Wakoma/nimble/assets/img/2-21.jpg

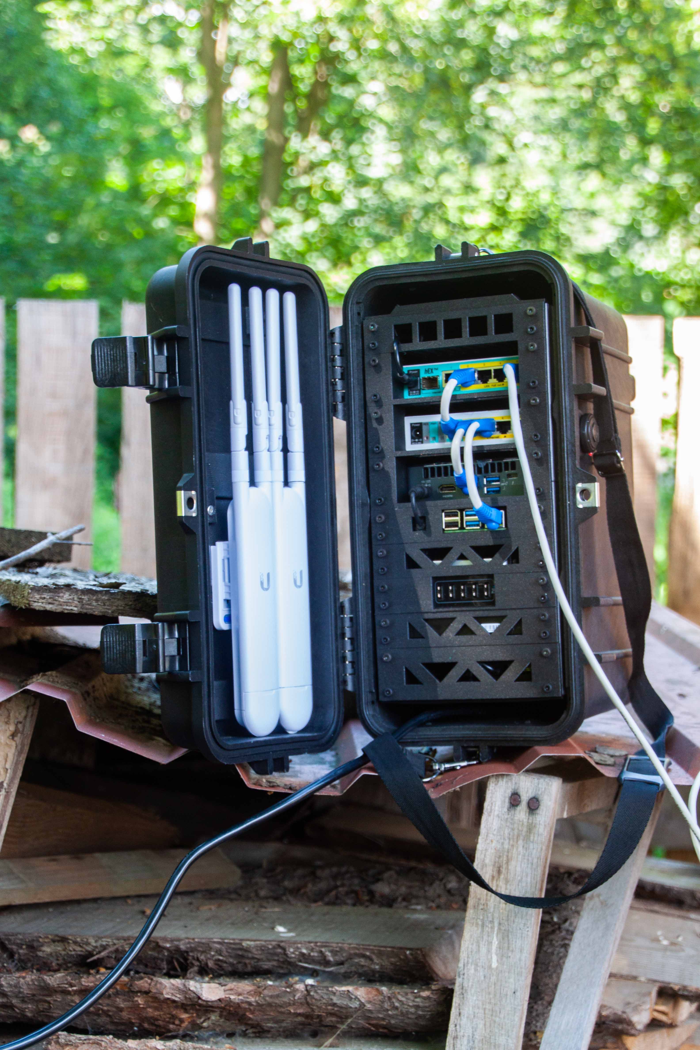
assets/img/2-21.jpg
