Wakoma/nimble/assets/img/3-4.jpg

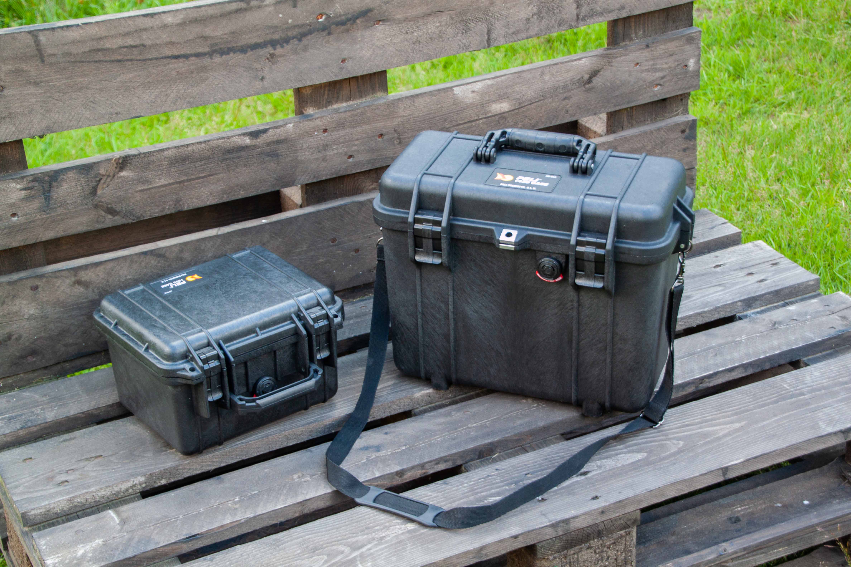
assets/img/3-4.jpg
