Wakoma/nimble/assets/img/12.jpg

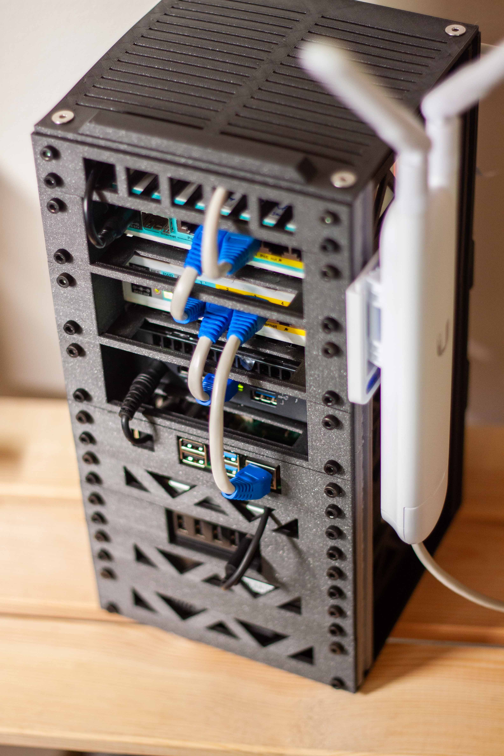
assets/img/12.jpg
