Wakoma/nimble/assets/img/16.jpg

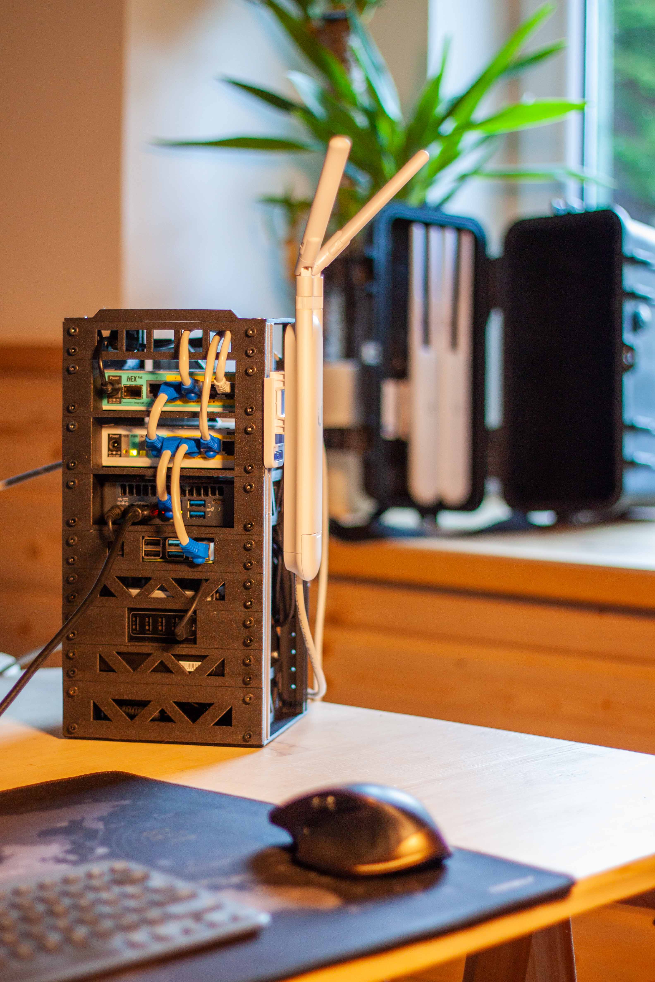
assets/img/16.jpg
