Wakoma/nimble/assets/img/18.jpg

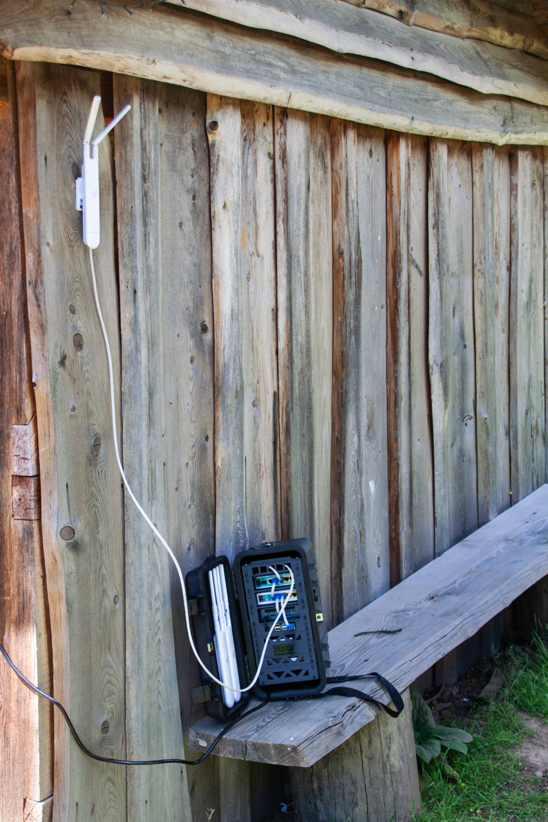
assets/img/18.jpg
