Wakoma/nimble/assets/img/LibreRouter/Carrousel-web/2.png

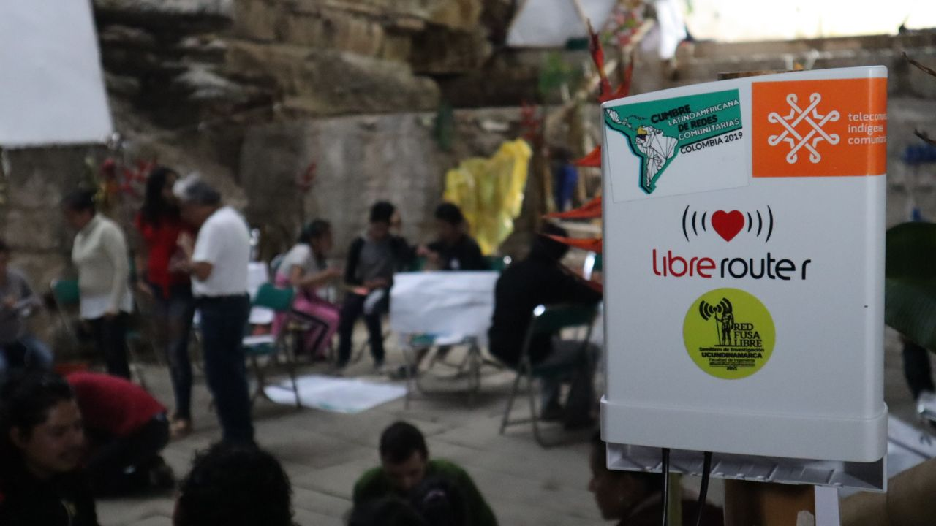
assets/img/LibreRouter/Carrousel-web/2.png
