Wakoma/nimble/assets/img/LibreRouter/Carrousel-web/3.png

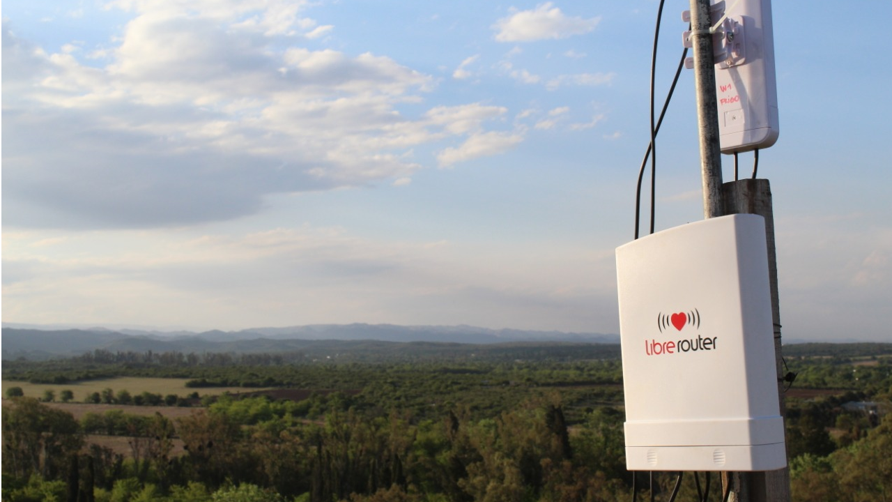
assets/img/LibreRouter/Carrousel-web/3.png
