Wakoma/nimble/assets/img/LibreRouter/Carrousel-web/5.png

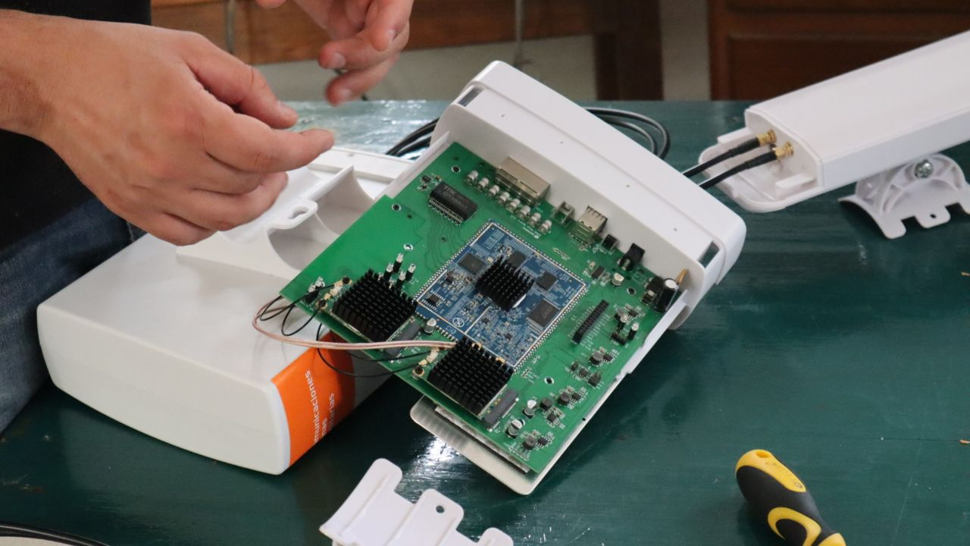
assets/img/LibreRouter/Carrousel-web/5.png
