Wakoma/nimble/assets/img/LibreRouter/Carrousel-web/6.png

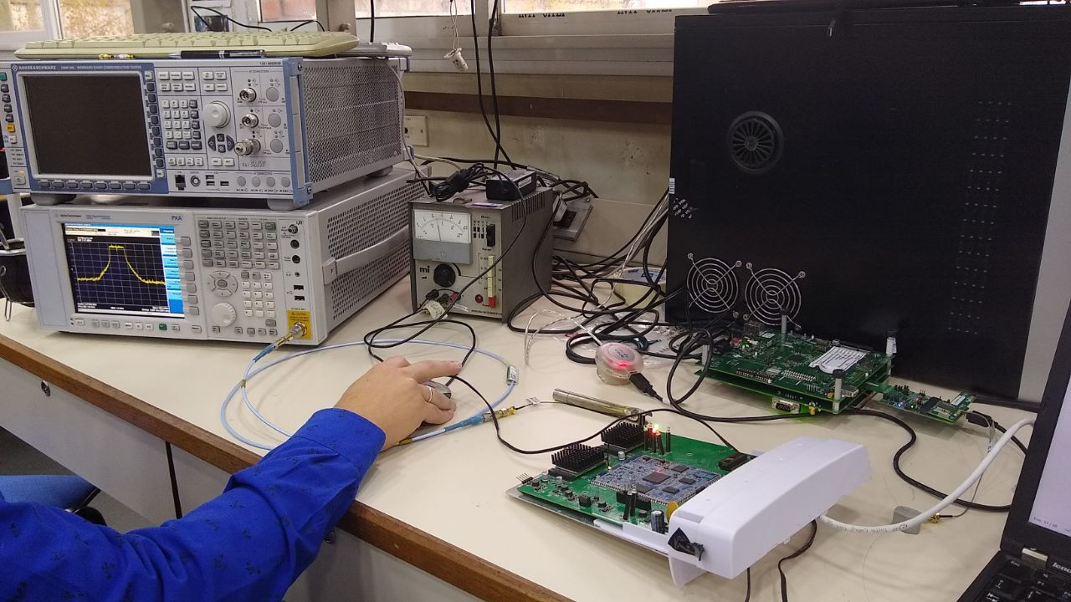
assets/img/LibreRouter/Carrousel-web/6.png
