Wakoma/nimble/assets/img/mesh.jpg

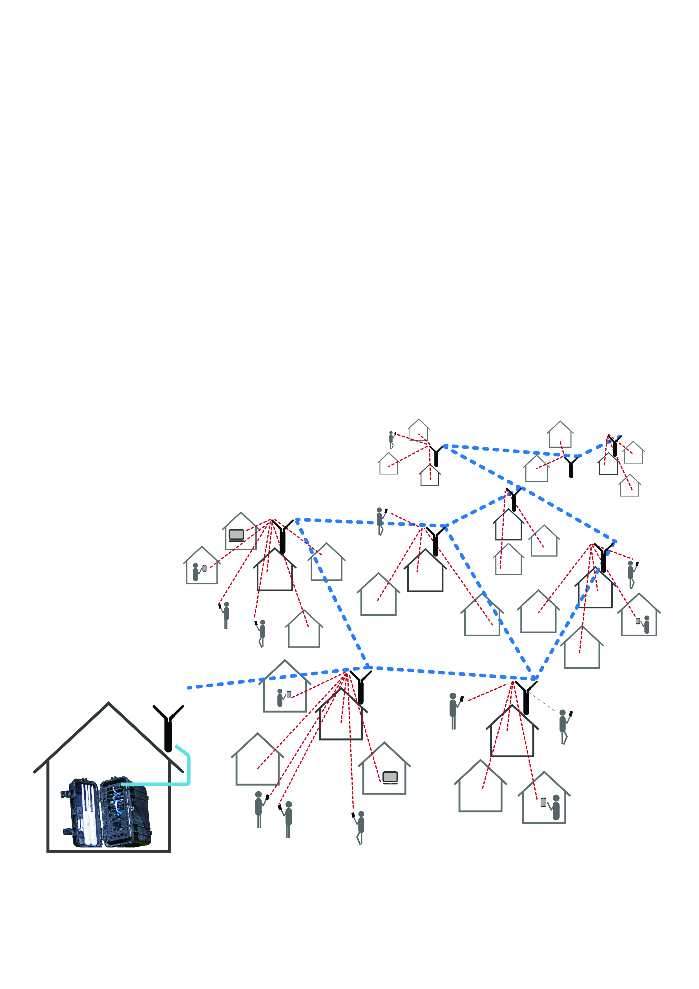
assets/img/mesh.jpg
