Wakoma/nimble/assets/img/Model_M/2.jpg

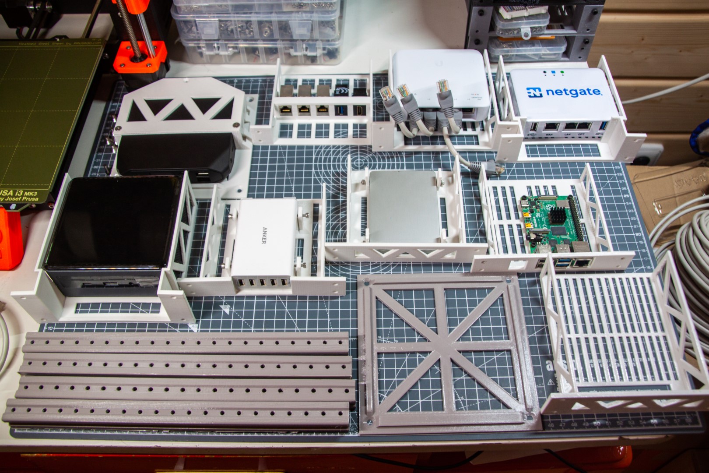
assets/img/Model_M/2.jpg
