Wakoma/nimble/assets/img/Model_M/3.jpg

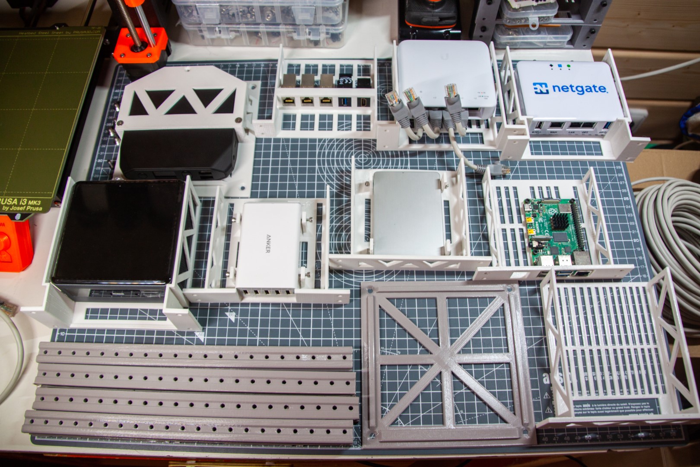
assets/img/Model_M/3.jpg
