Wakoma/nimble/assets/img/Model_M/4.jpg

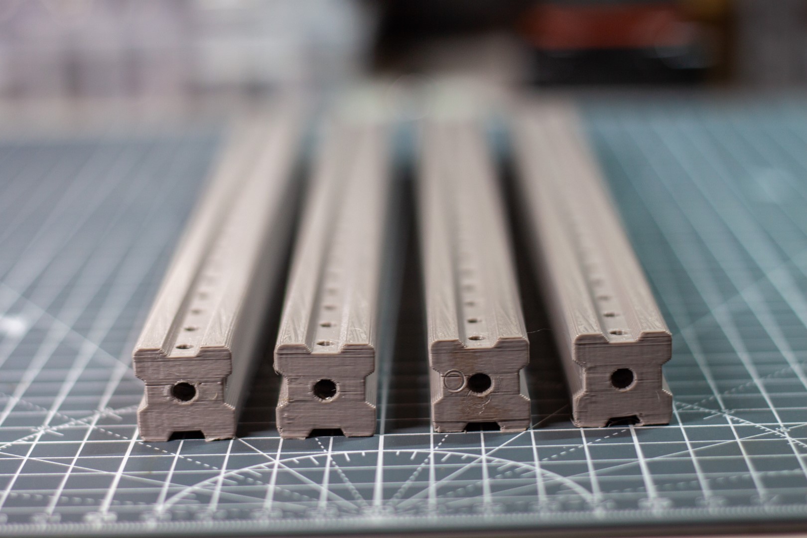
assets/img/Model_M/4.jpg
