Wakoma/nimble/assets/img/Model_M/5.jpg

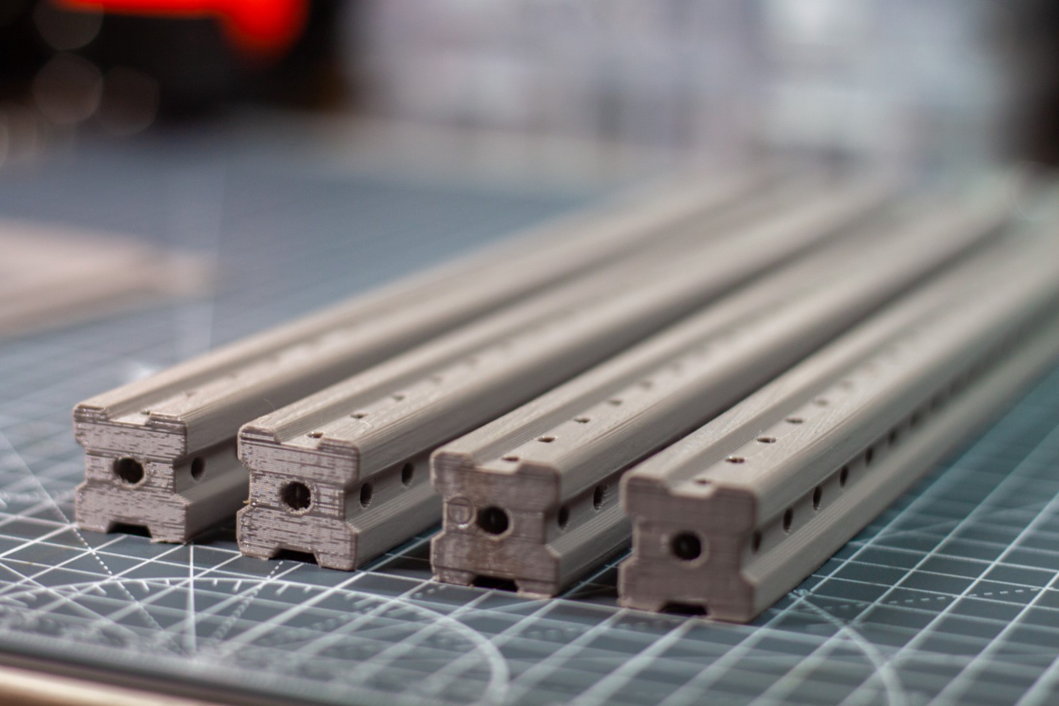
assets/img/Model_M/5.jpg
