Wakoma/nimble/assets/img/Model_M/6.jpg

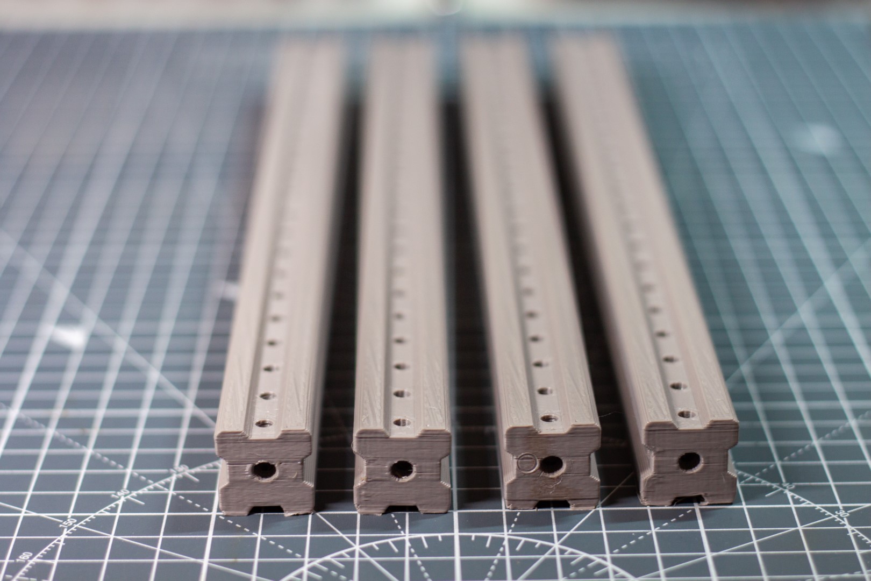
assets/img/Model_M/6.jpg
