Wakoma/nimble/assets/img/Model_M/7.jpg

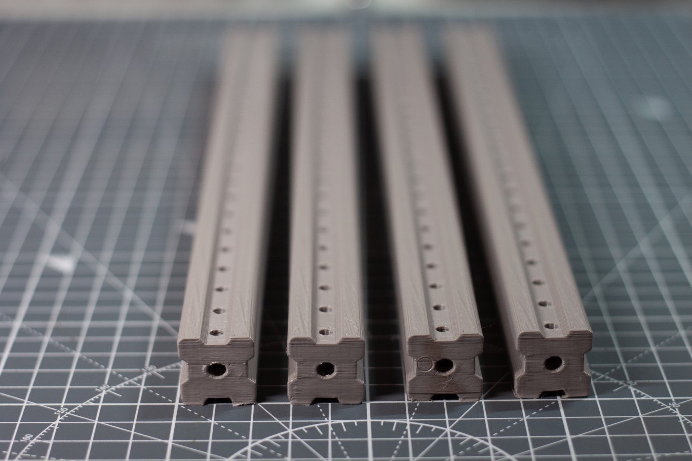
assets/img/Model_M/7.jpg
