Wakoma/nimble/assets/img/Model_M/8.jpg

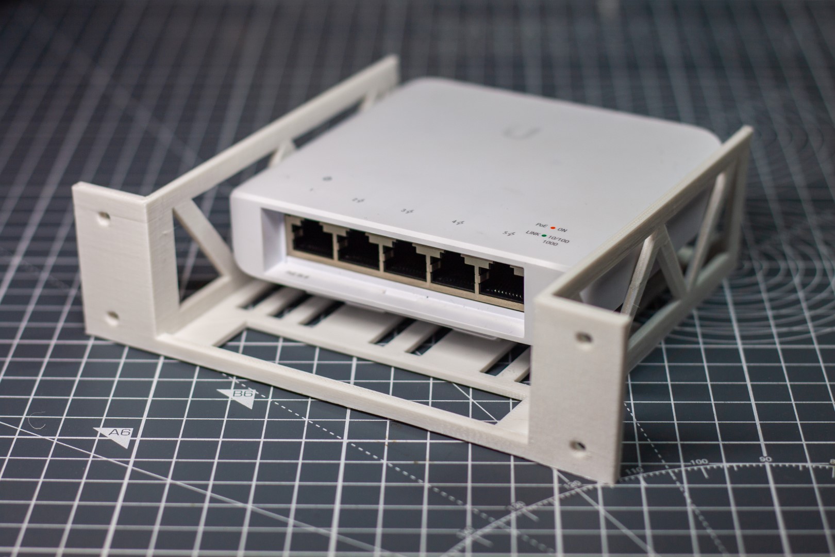
assets/img/Model_M/8.jpg
