Wakoma/nimble/assets/img/Model_M/9.jpg

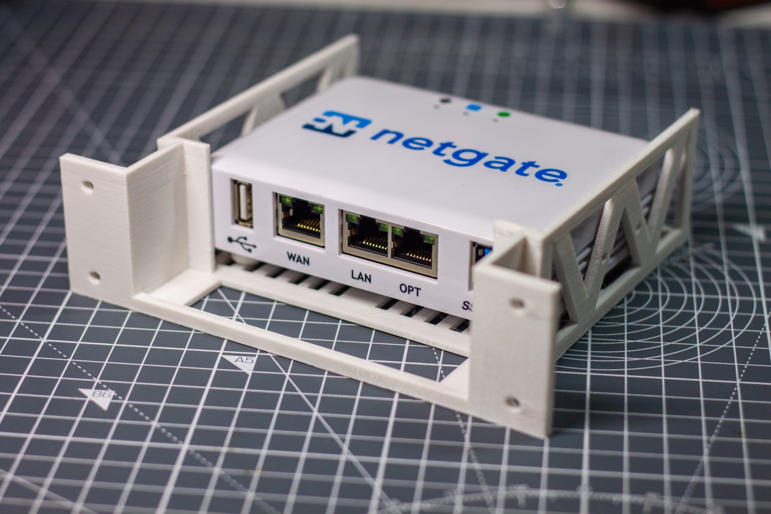
assets/img/Model_M/9.jpg
