Wakoma/nimble/assets/img/Model_M/10.jpg

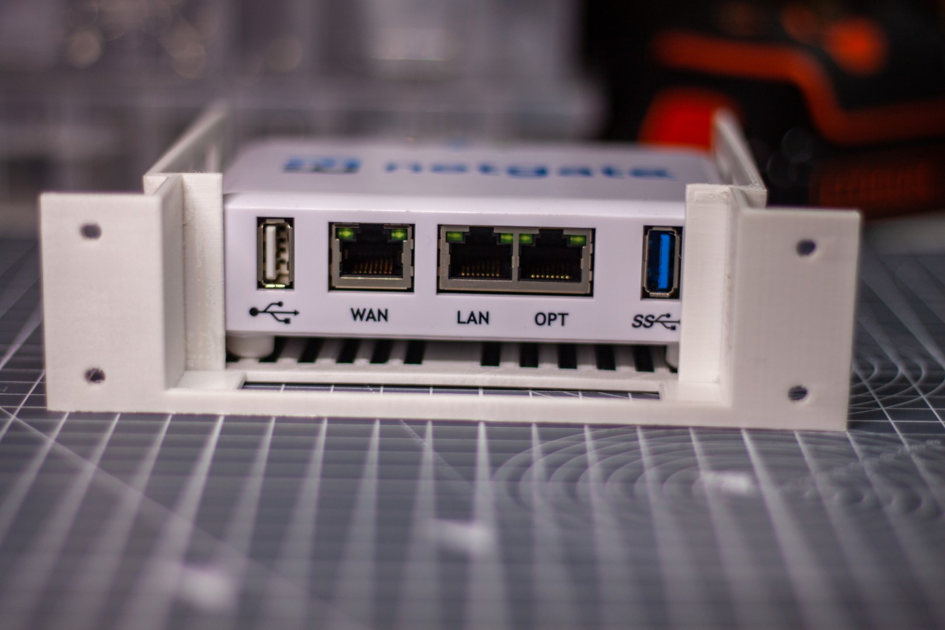
assets/img/Model_M/10.jpg
