Wakoma/nimble/assets/img/Model_M/11.jpg

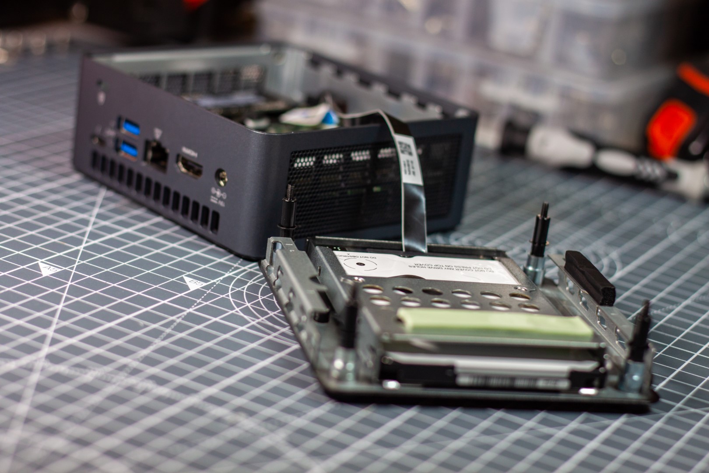
assets/img/Model_M/11.jpg
