Wakoma/nimble/assets/img/Model_M/12.jpg

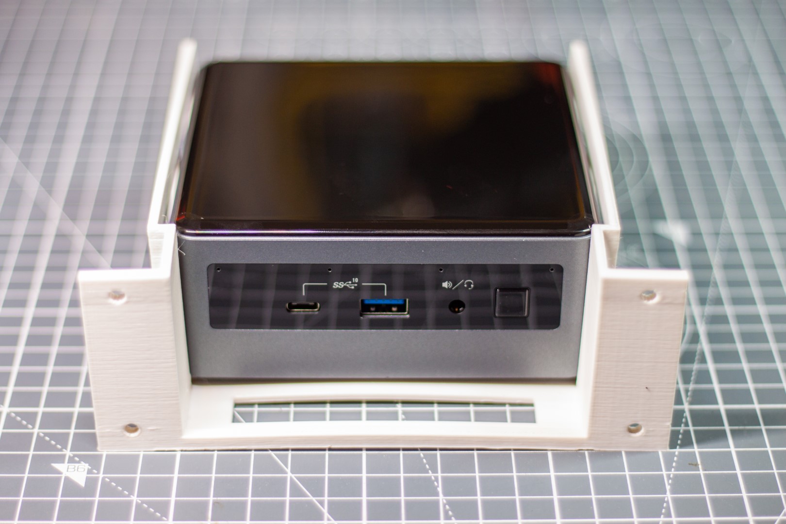
assets/img/Model_M/12.jpg
