Wakoma/nimble/assets/img/Model_M/13.jpg

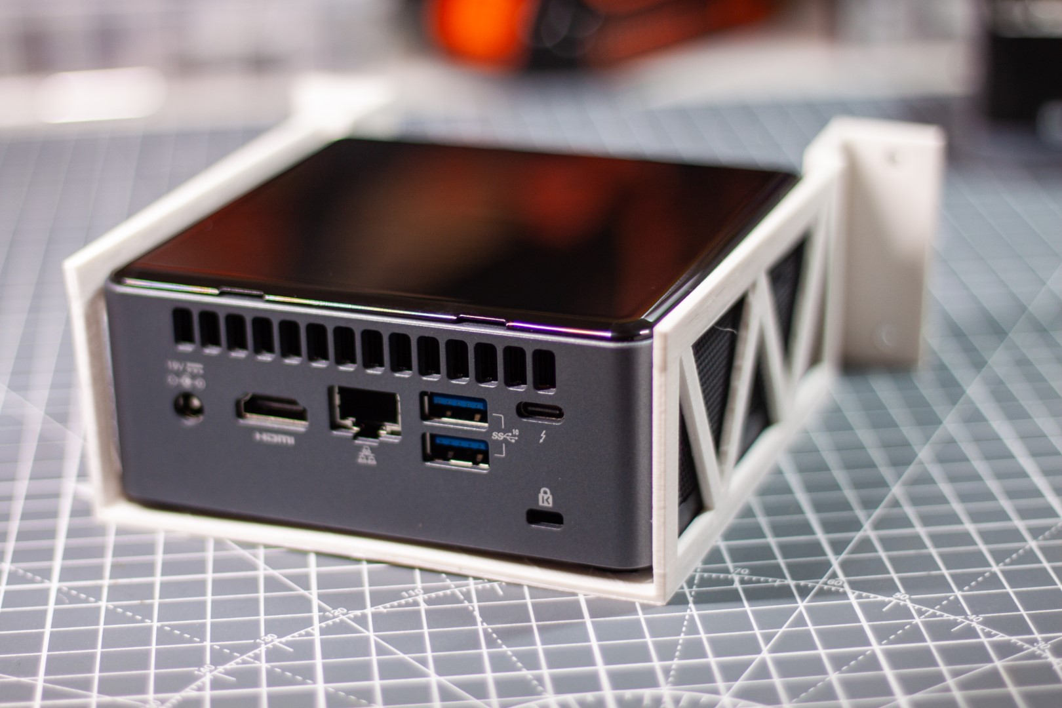
assets/img/Model_M/13.jpg
