Wakoma/nimble/assets/img/Model_M/14.jpg

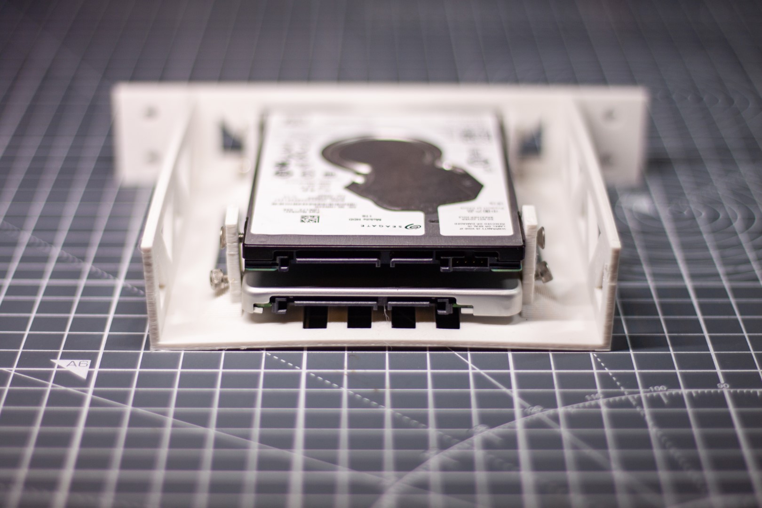
assets/img/Model_M/14.jpg
