Wakoma/nimble/assets/img/Model_M/15.jpg

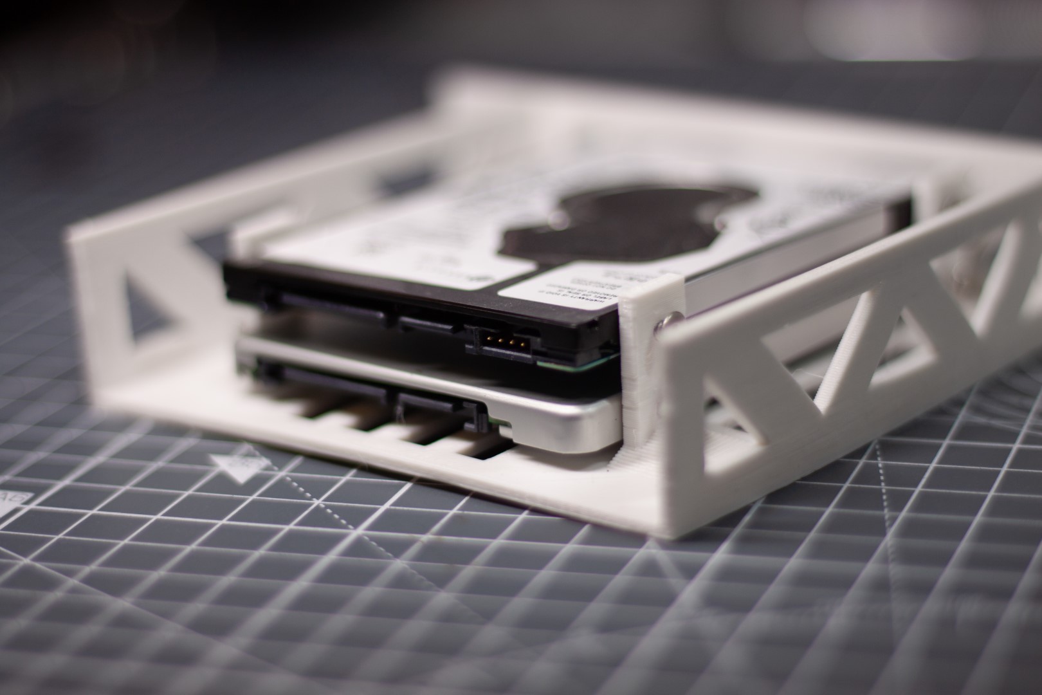
assets/img/Model_M/15.jpg
