Wakoma/nimble/assets/img/Model_M/16.jpg

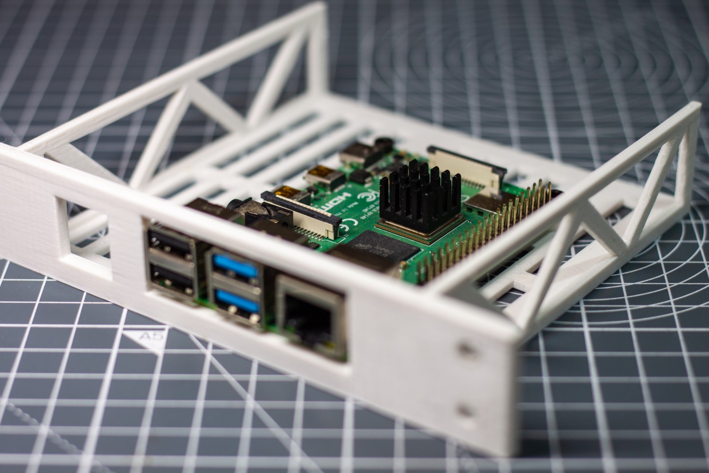
assets/img/Model_M/16.jpg
