Wakoma/nimble/assets/img/Model_M/17.jpg

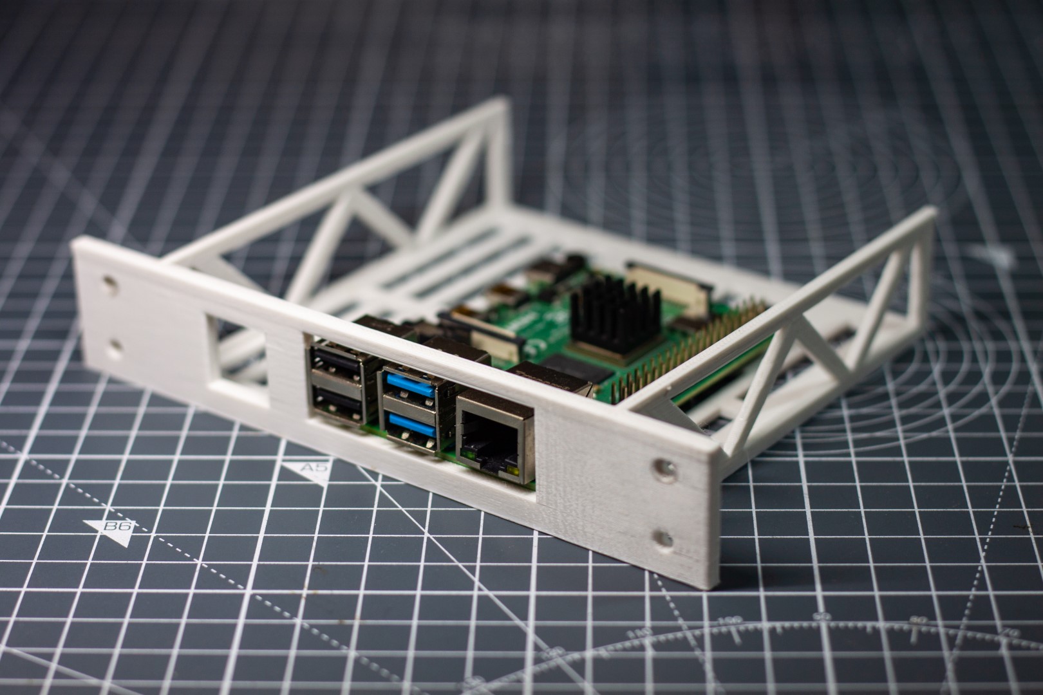
assets/img/Model_M/17.jpg
