Wakoma/nimble/assets/img/Model_M/18.jpg

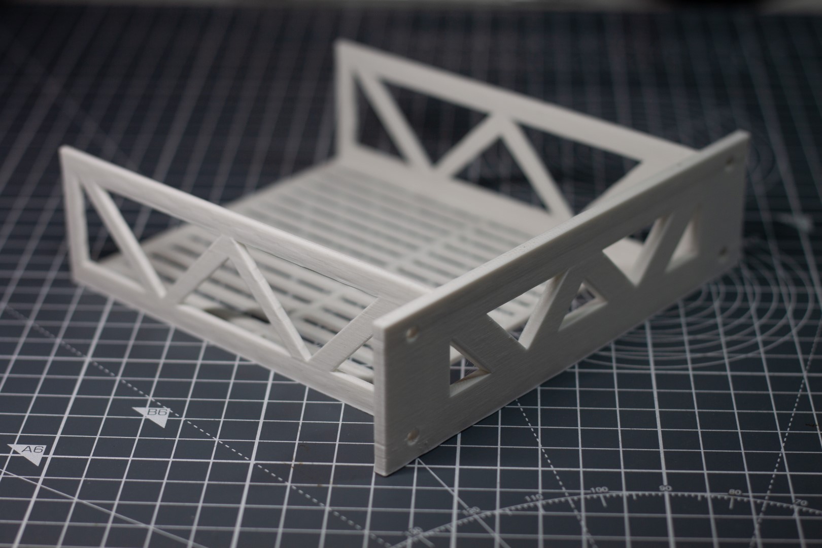
assets/img/Model_M/18.jpg
