Wakoma/nimble/assets/img/Model_M/19.jpg

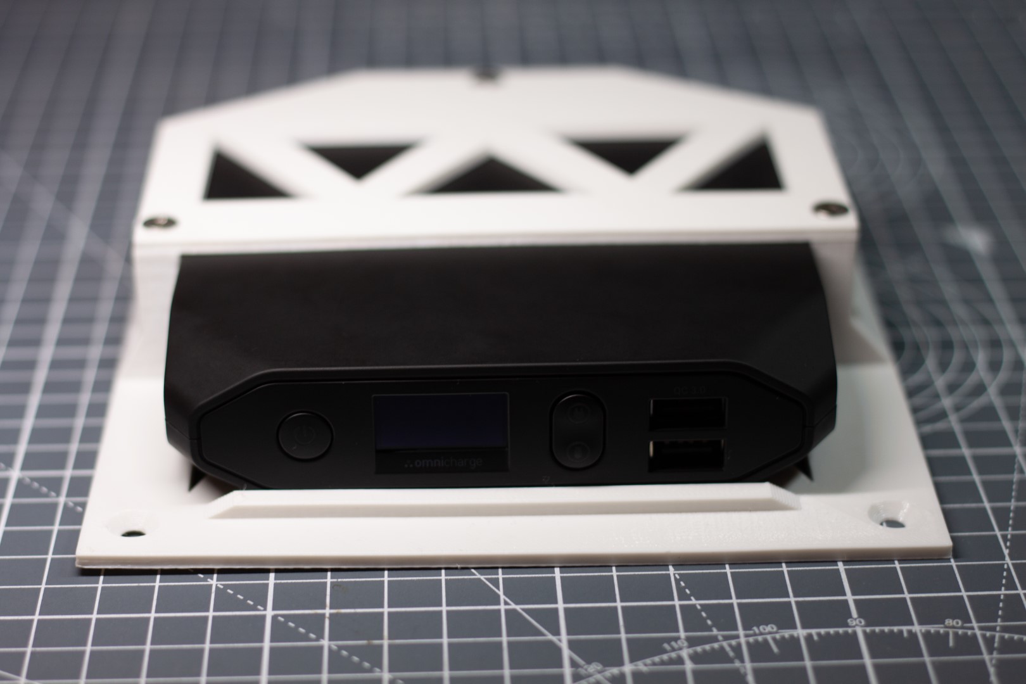
assets/img/Model_M/19.jpg
