Wakoma/nimble/assets/img/Model_M/20.jpg

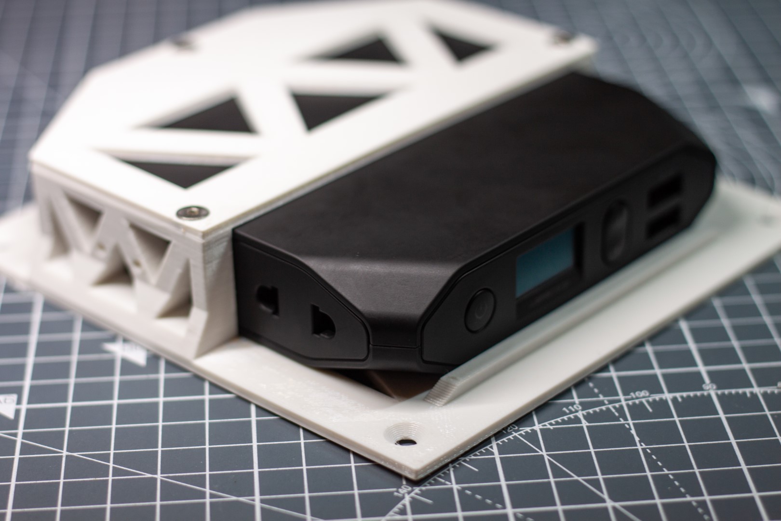
assets/img/Model_M/20.jpg
