Wakoma/nimble/assets/img/Model_M/21.jpg

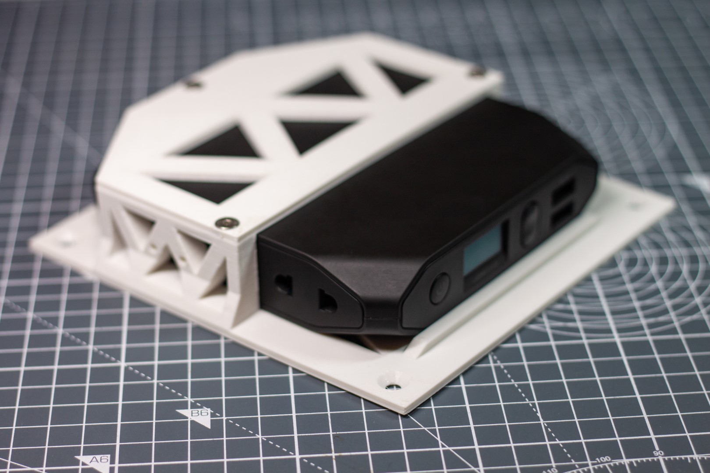
assets/img/Model_M/21.jpg
