Wakoma/nimble/assets/img/Model_M/22.jpg

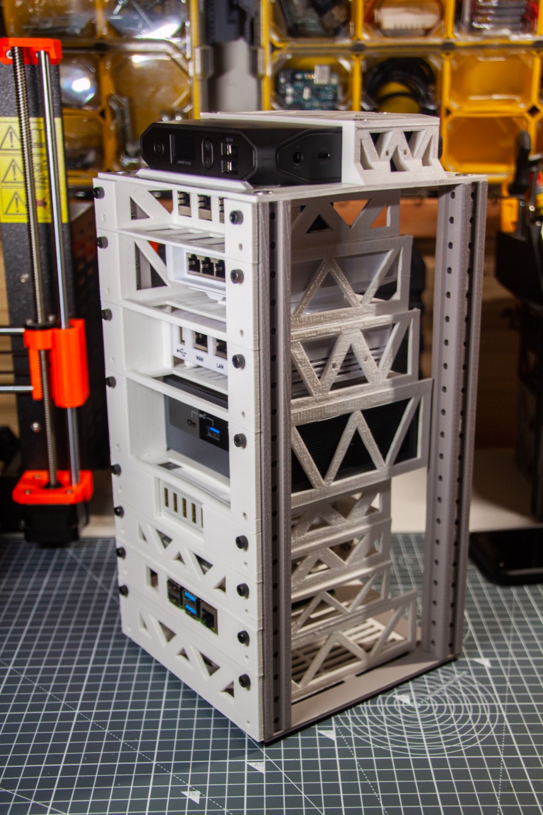
assets/img/Model_M/22.jpg
