Wakoma/nimble/assets/img/Model_M/23.jpg

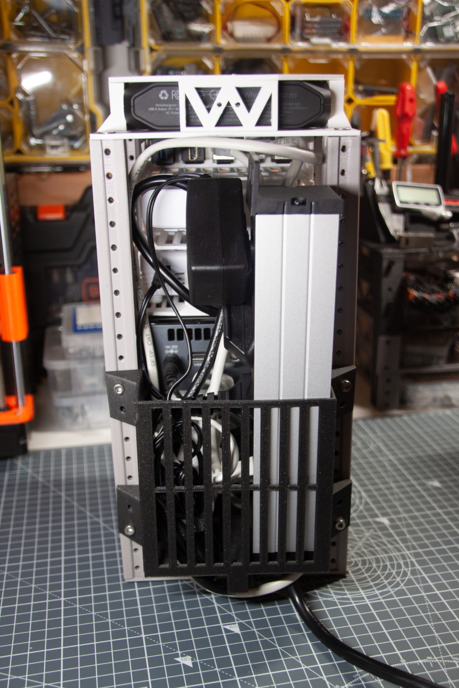
assets/img/Model_M/23.jpg
