Wakoma/nimble/assets/img/Model_M/24.jpg

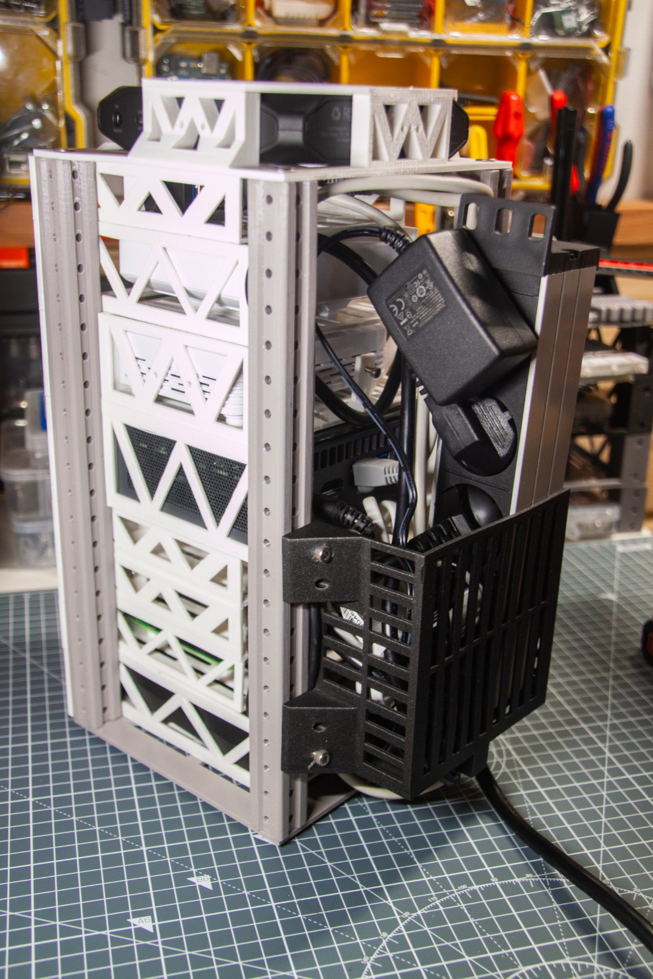
assets/img/Model_M/24.jpg
