Wakoma/nimble/assets/img/Model_M/25.jpg

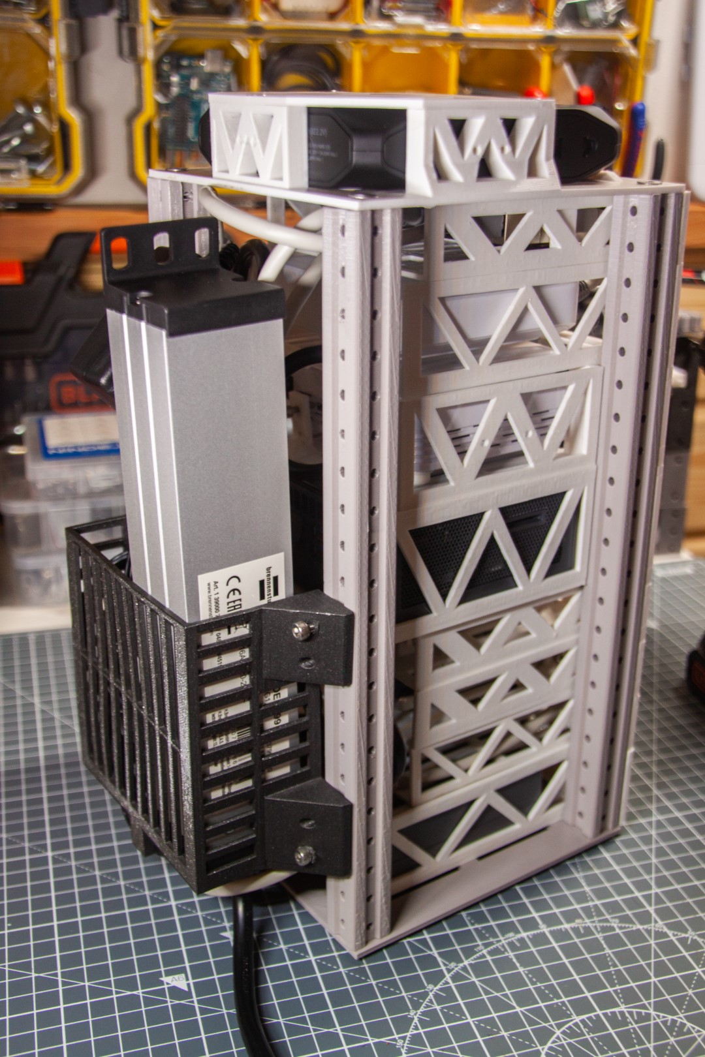
assets/img/Model_M/25.jpg
