Wakoma/nimble/assets/img/Model_M/26.jpg

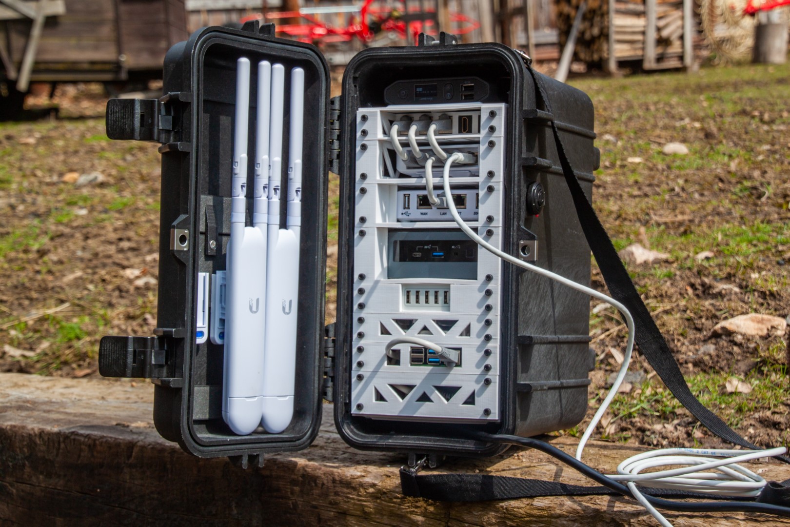
assets/img/Model_M/26.jpg
