Wakoma/nimble/assets/img/Model_M/27.jpg

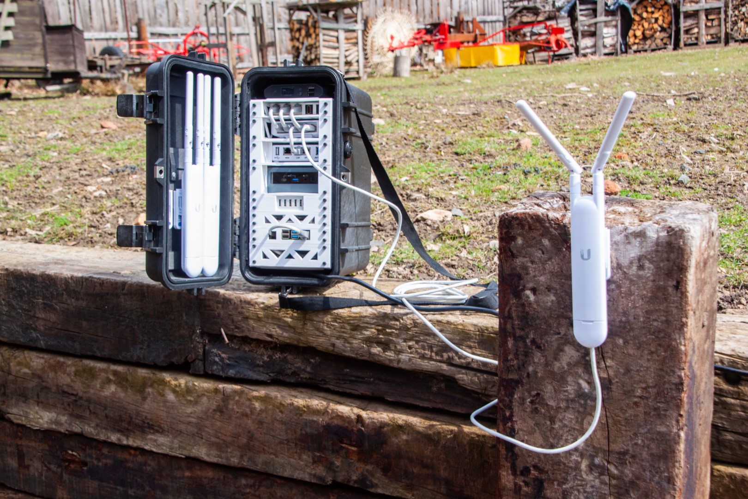
assets/img/Model_M/27.jpg
