Wakoma/nimble/assets/img/Model_M/28.jpg

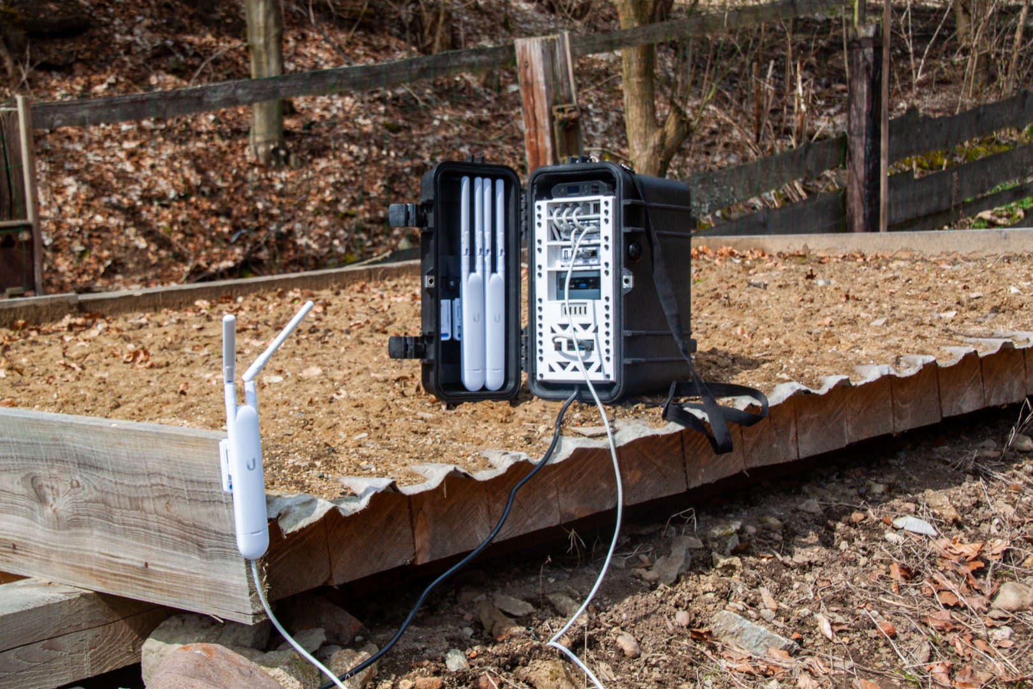
assets/img/Model_M/28.jpg
