Wakoma/nimble/assets/img/Model_M/29.jpg

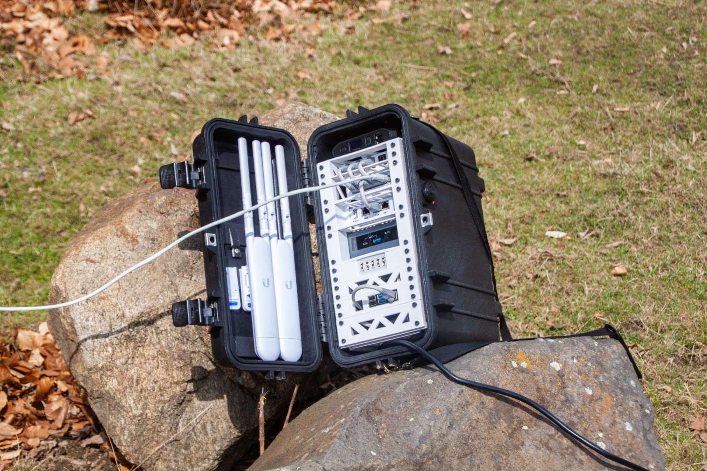
assets/img/Model_M/29.jpg
