Wakoma/nimble/assets/img/Model_M/30.jpg

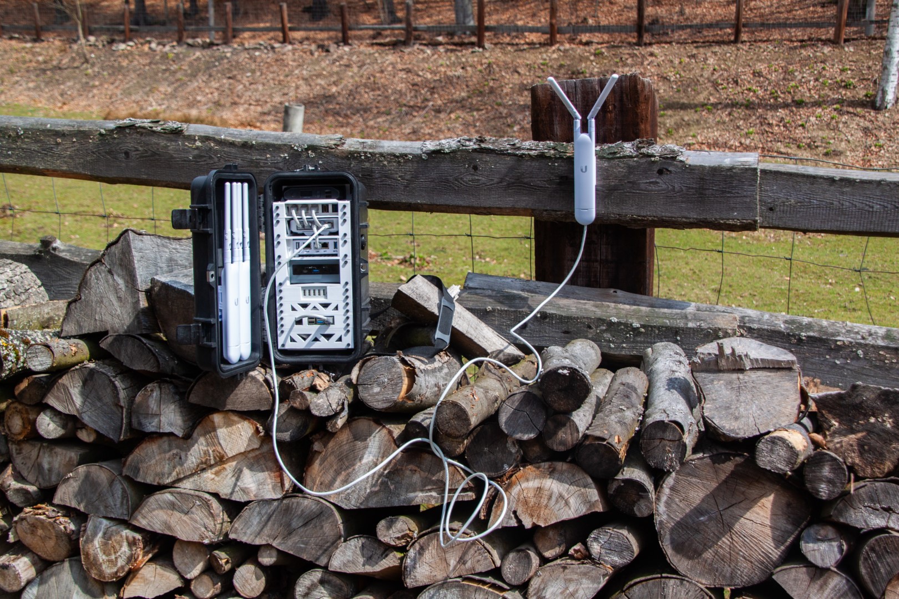
assets/img/Model_M/30.jpg
