Wakoma/nimble/assets/img/Model_M/31.jpg

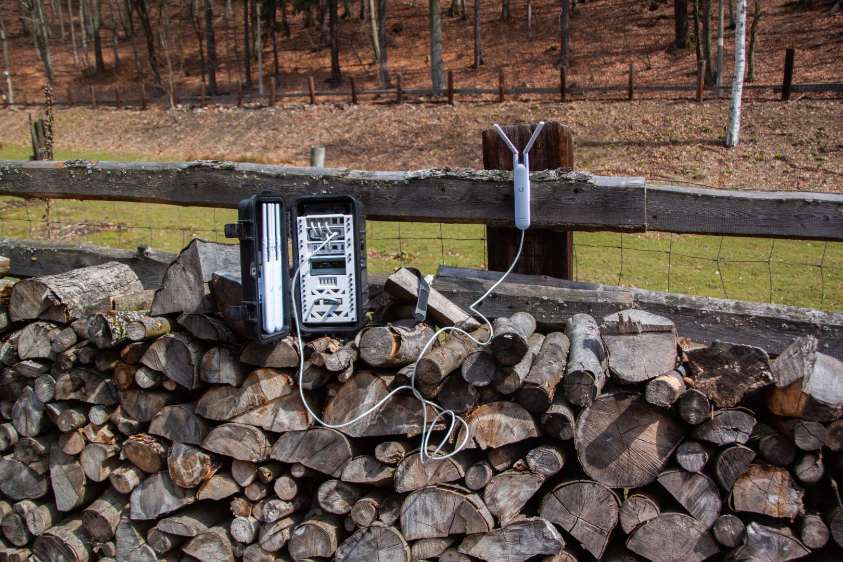
assets/img/Model_M/31.jpg
