Wakoma/nimble/assets/img/Model_M/32.jpg

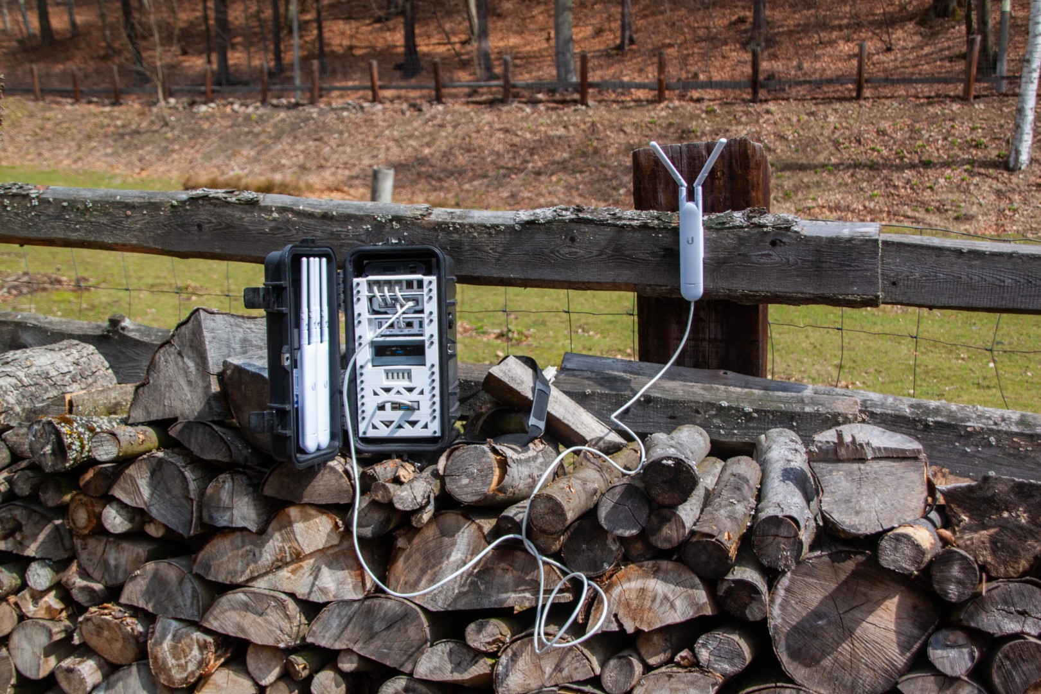
assets/img/Model_M/32.jpg
