Wakoma/nimble/assets/img/Model_M/33.jpg

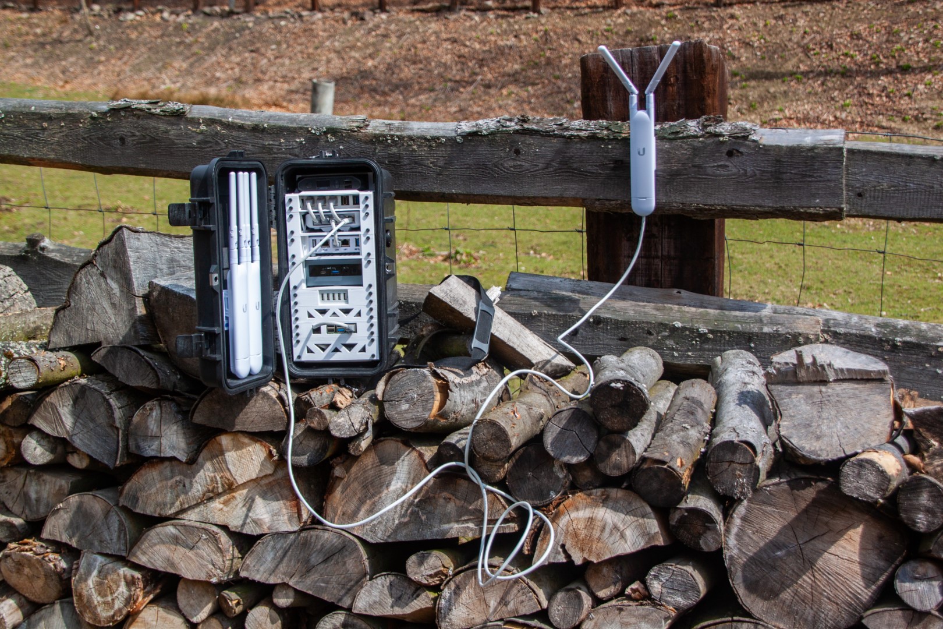
assets/img/Model_M/33.jpg
