Wakoma/nimble/assets/img/Model_M/34.jpg

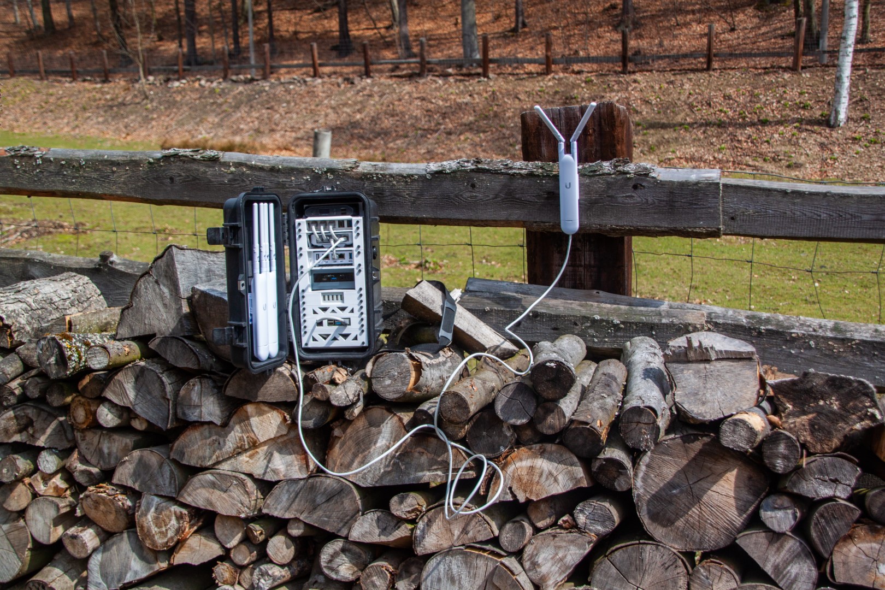
assets/img/Model_M/34.jpg
