Wakoma/nimble/assets/img/Model_M/37.jpg

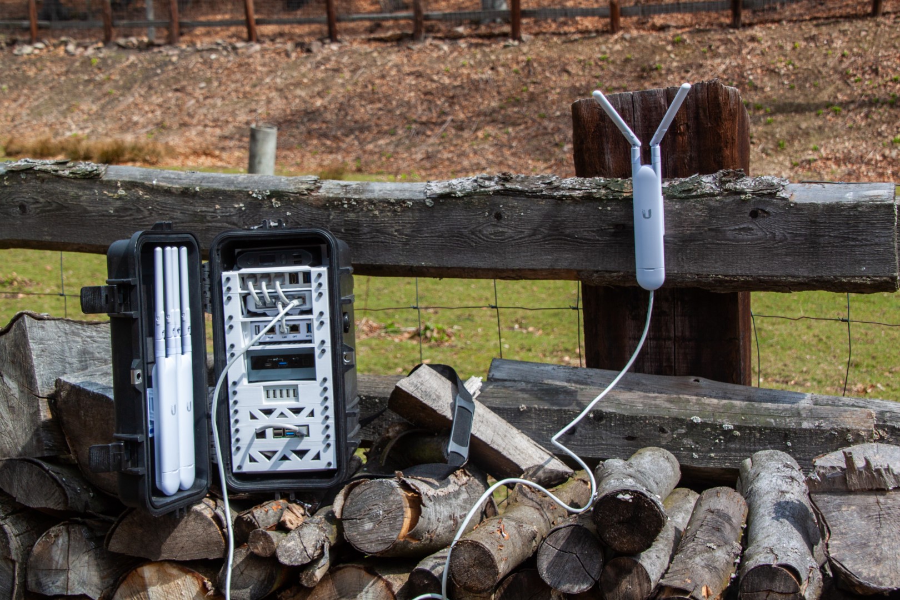
assets/img/Model_M/37.jpg
