Wakoma/nimble/assets/img/Model_M/38.jpg

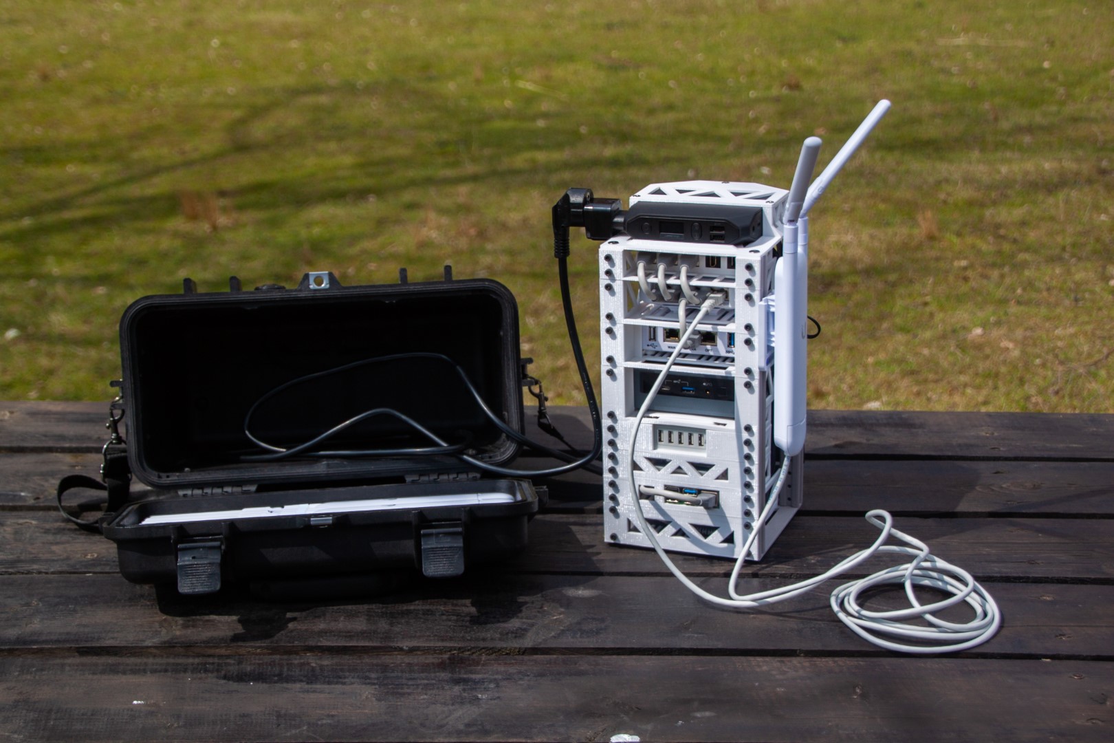
assets/img/Model_M/38.jpg
