Wakoma/nimble/assets/img/Model_M/39.jpg

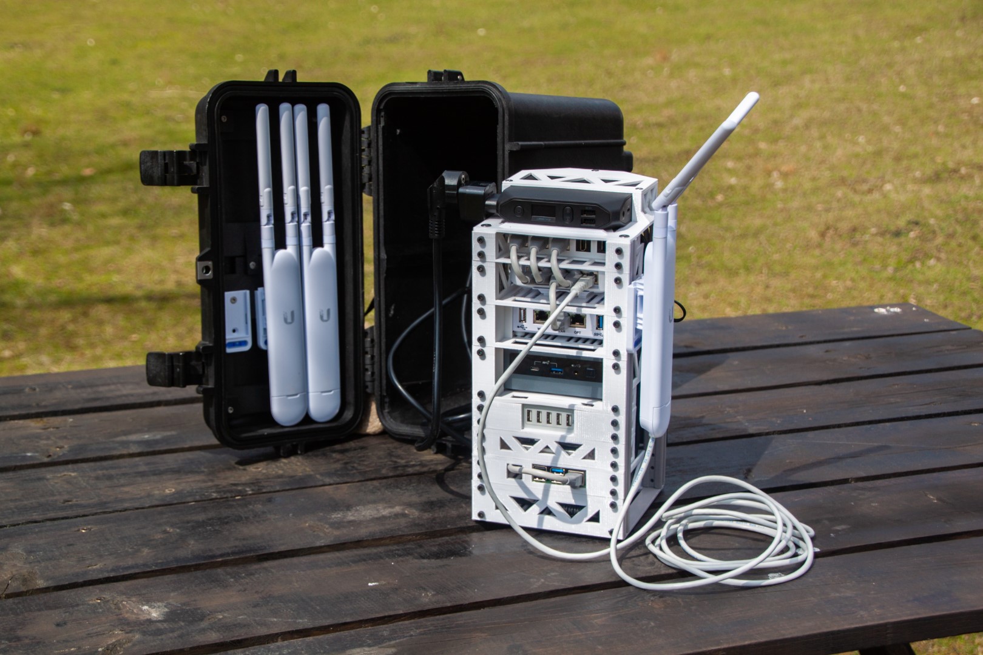
assets/img/Model_M/39.jpg
