Wakoma/nimble/assets/img/Model_M/40.jpg

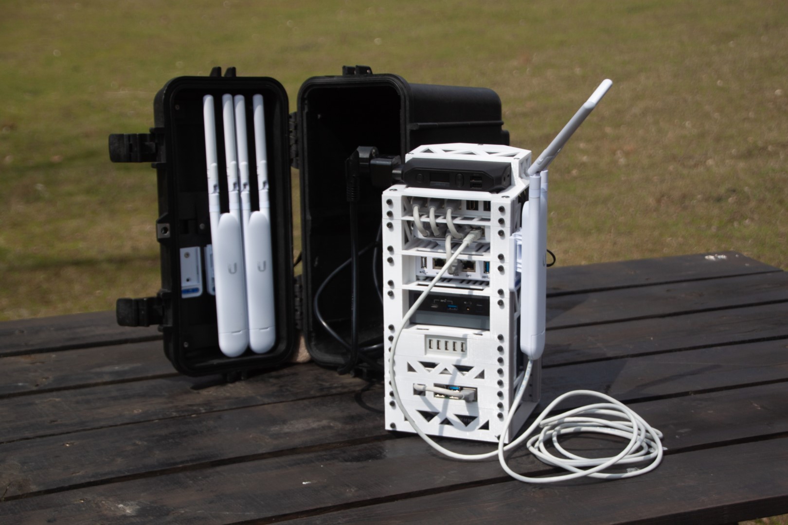
assets/img/Model_M/40.jpg
