Wakoma/nimble/assets/img/Model_M/41.jpg

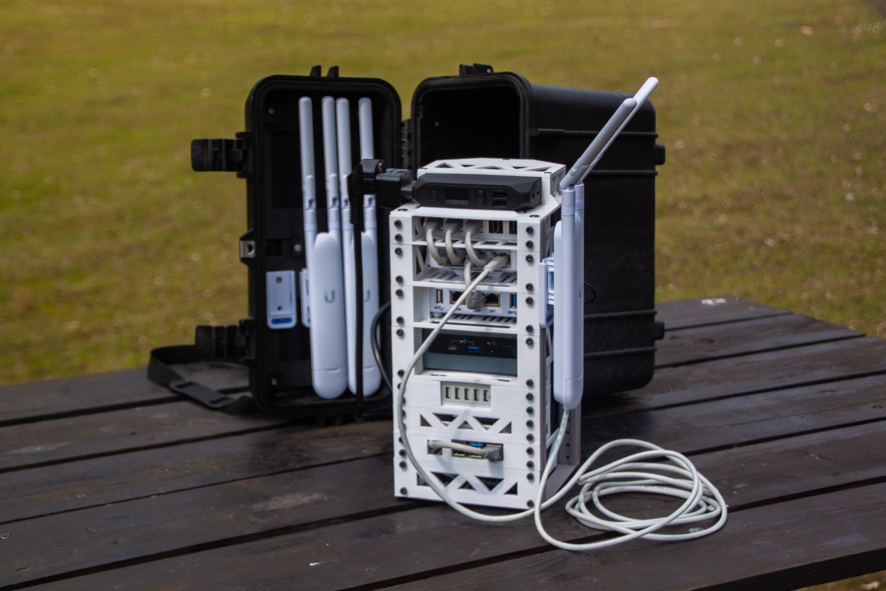
assets/img/Model_M/41.jpg
