Wakoma/nimble/assets/img/Model_M/42.jpg

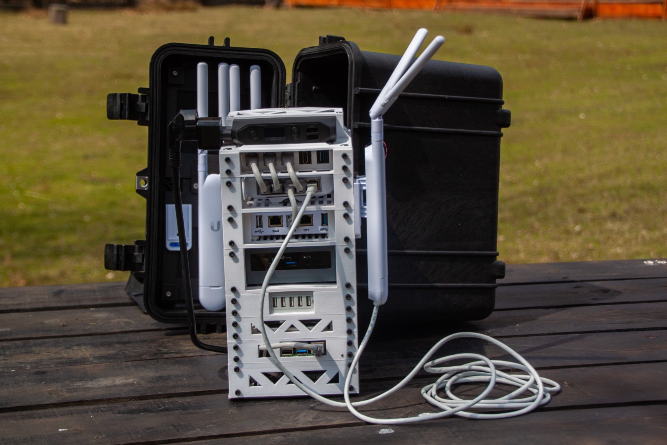
assets/img/Model_M/42.jpg
