Wakoma/nimble/assets/img/Network_Hardware/1514_l.jpg

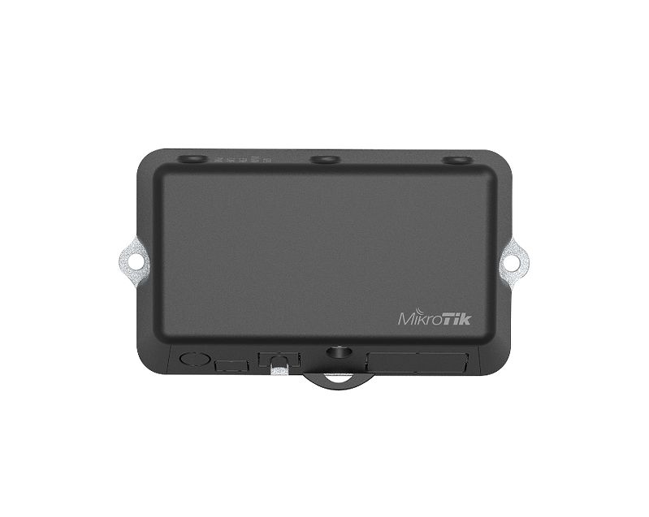
assets/img/Network_Hardware/1514_l.jpg
