Wakoma/nimble/assets/img/Network_Hardware/flex.webp

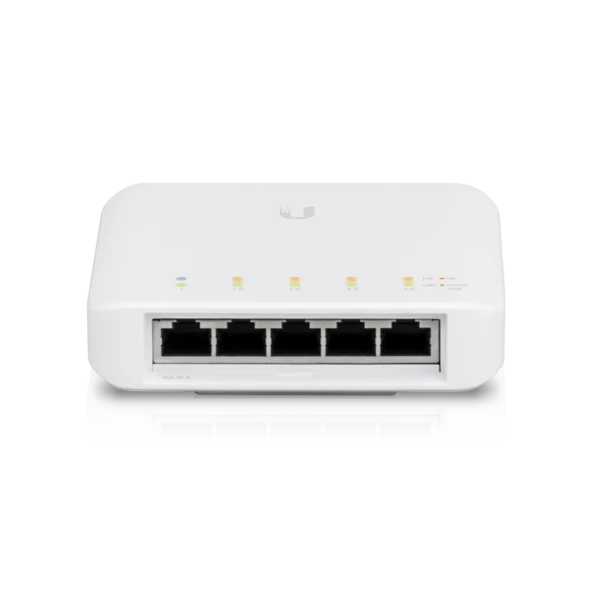
assets/img/Network_Hardware/flex.webp
