Wakoma/nimble/assets/img/Network_Hardware/omnipng.png

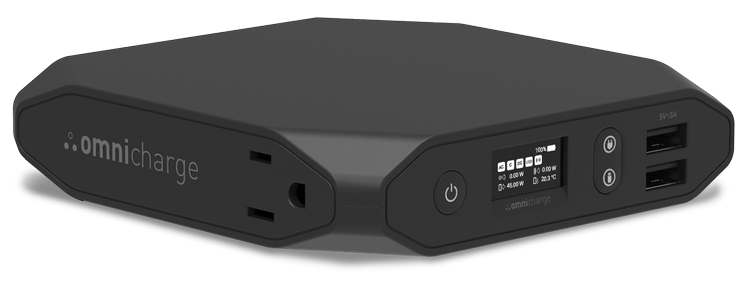
assets/img/Network_Hardware/omnipng.png
