Wakoma/nimble/assets/img/Network_Hardware/power3.webp

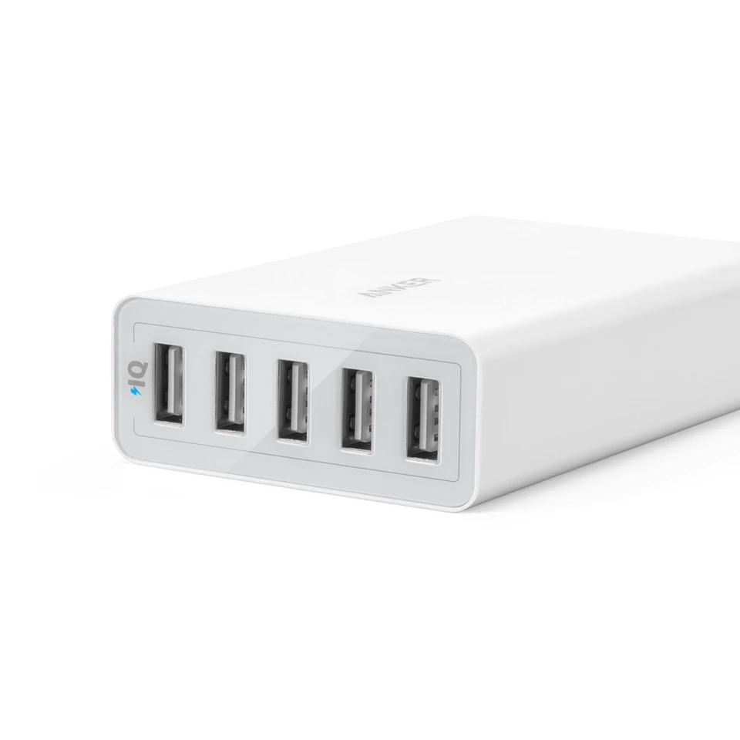
assets/img/Network_Hardware/power3.webp
