Wakoma/nimble/assets/img/Network_Hardware/power4.jpg

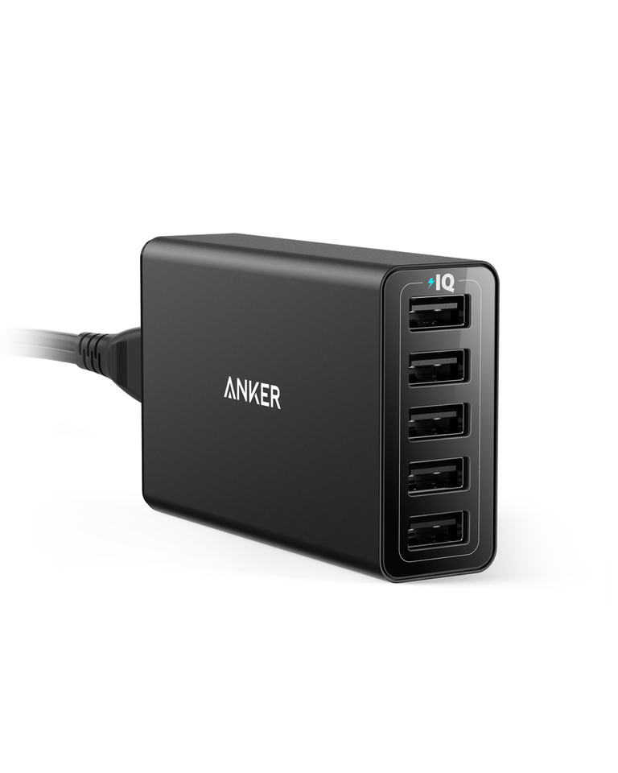
assets/img/Network_Hardware/power4.jpg
