Wakoma/nimble/assets/img/Network_Hardware/powerport.jpg

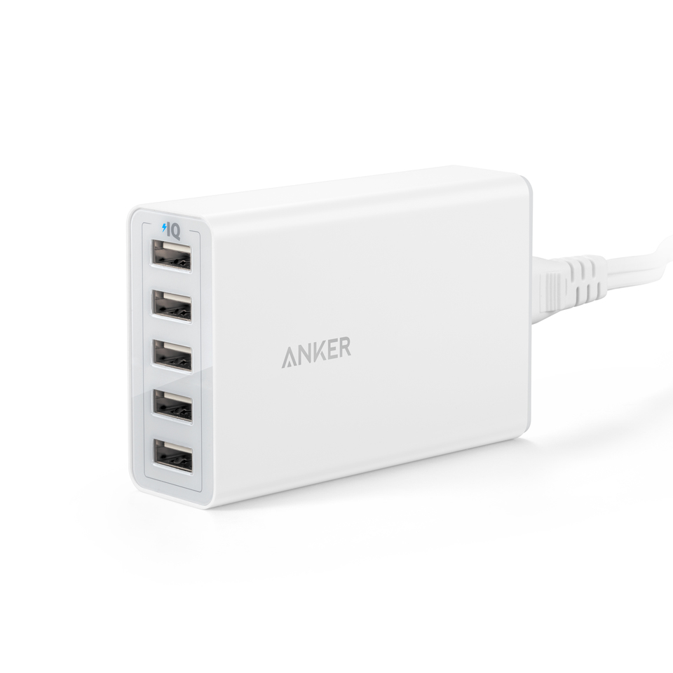
assets/img/Network_Hardware/powerport.jpg
