Wakoma/nimble/assets/img/Network_Hardware/powerstrip.jpg

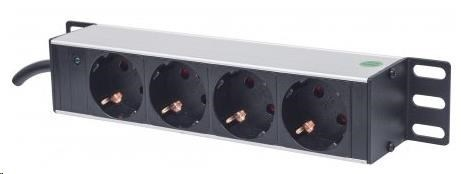
assets/img/Network_Hardware/powerstrip.jpg
