Wakoma/nimble/assets/img/Network_Hardware/rpi.png

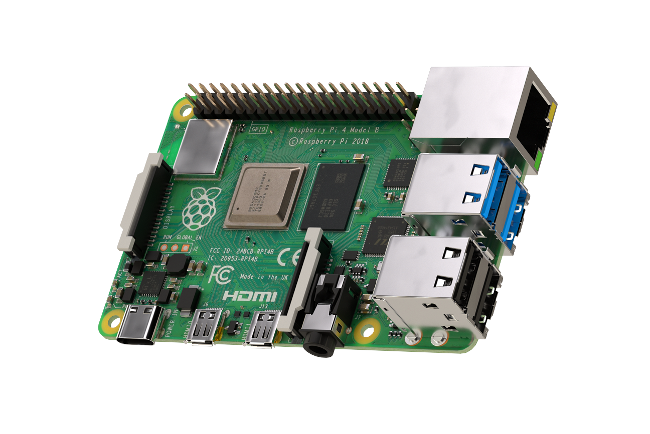
assets/img/Network_Hardware/rpi.png
