Wakoma/nimble/assets/img/Network_Hardware/Sg-1100.webp

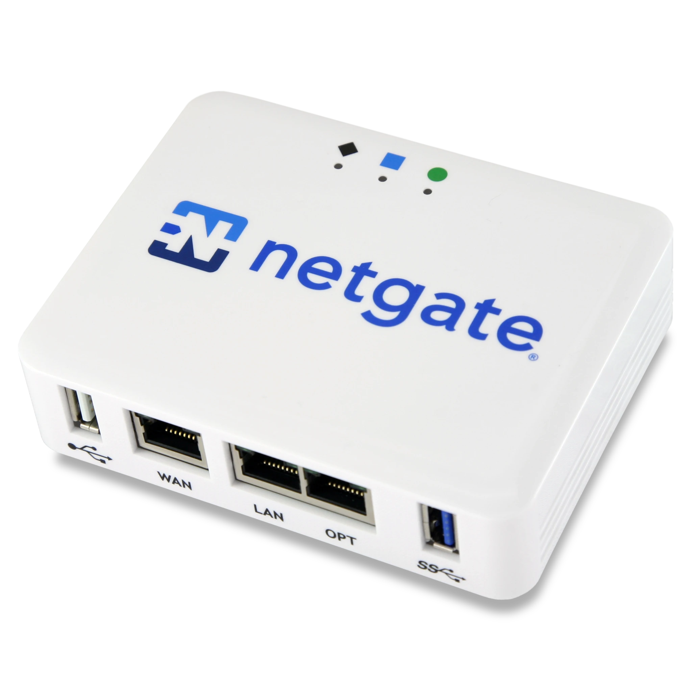
assets/img/Network_Hardware/Sg-1100.webp
