Wakoma/nimble/assets/img/Network_Hardware/UBI_POE-50-60W_01.png

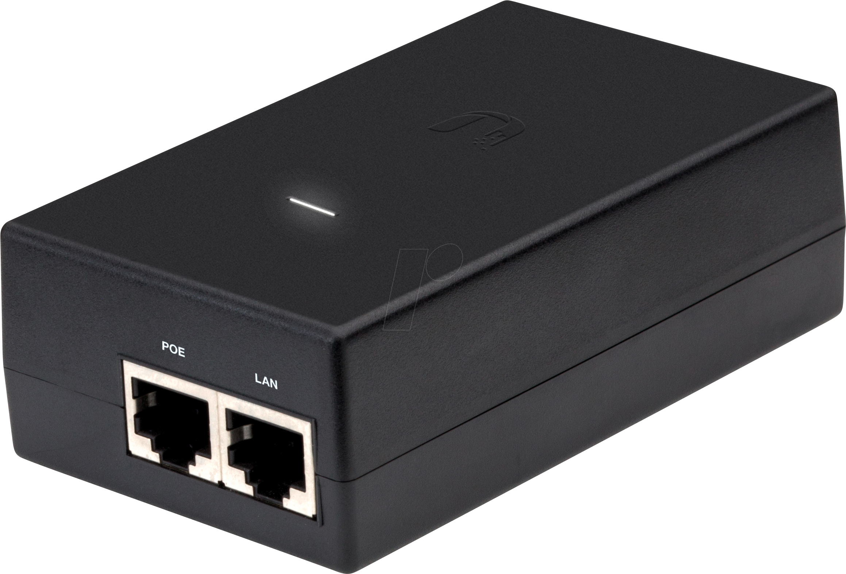
assets/img/Network_Hardware/UBI_POE-50-60W_01.png
