Wakoma/nimble/assets/img/nimblemesh zoomed.jpg

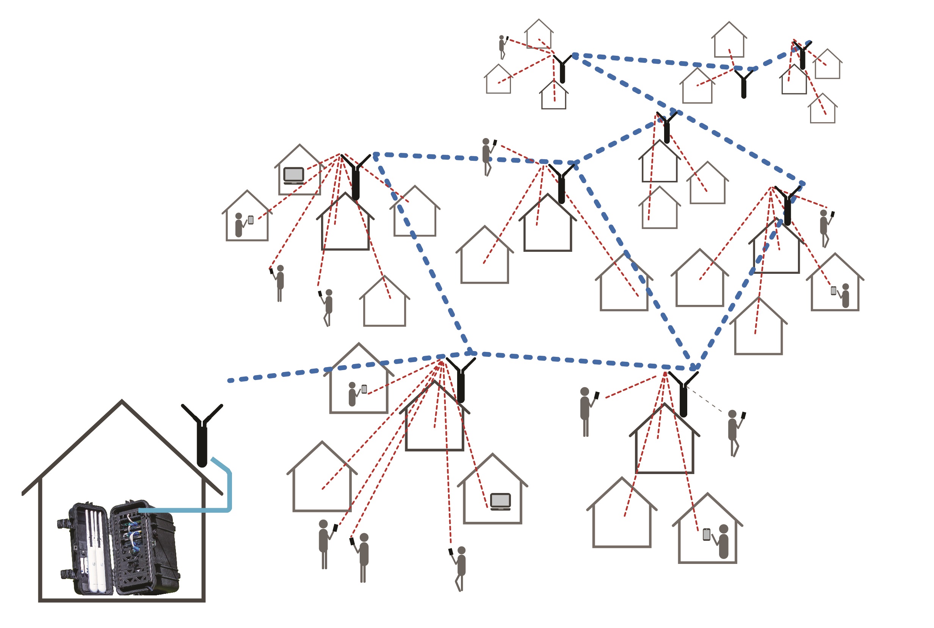
assets/img/nimblemesh zoomed.jpg
