Wakoma/nimble/assets/img/OTFNhackathon.jpeg

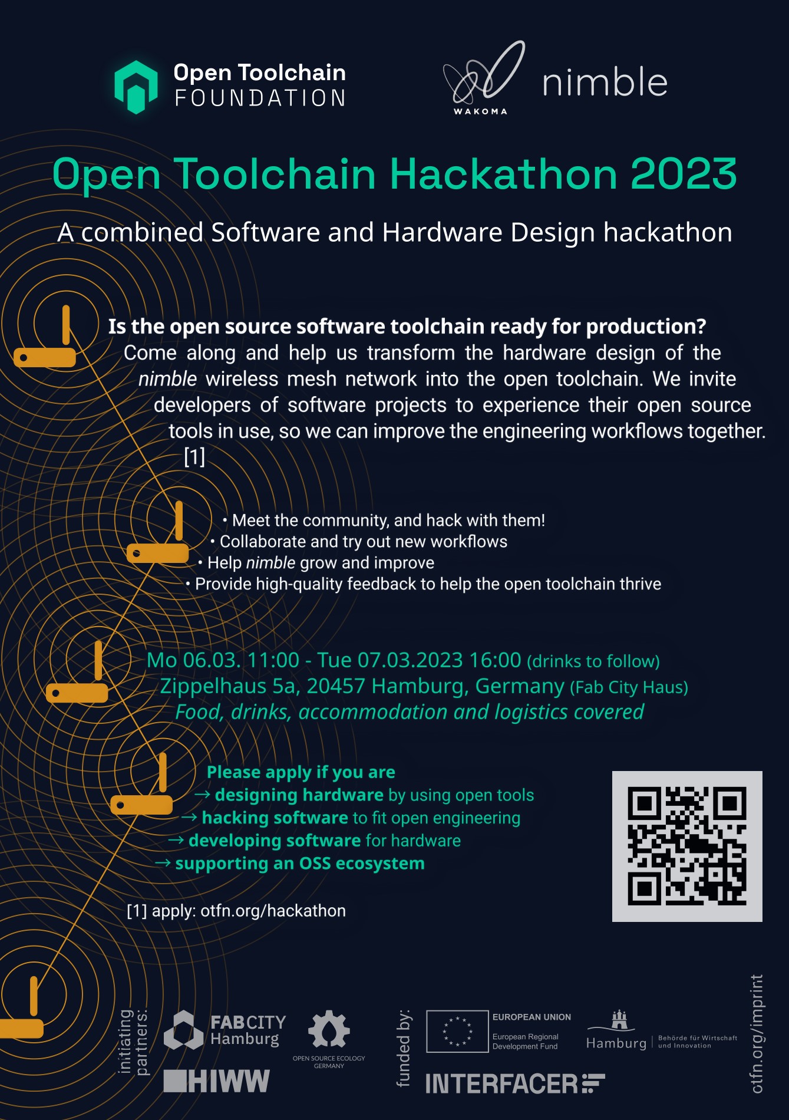
assets/img/OTFNhackathon.jpeg
