Wakoma/nimble/gen/mech/ltap_mini_shallow.stl

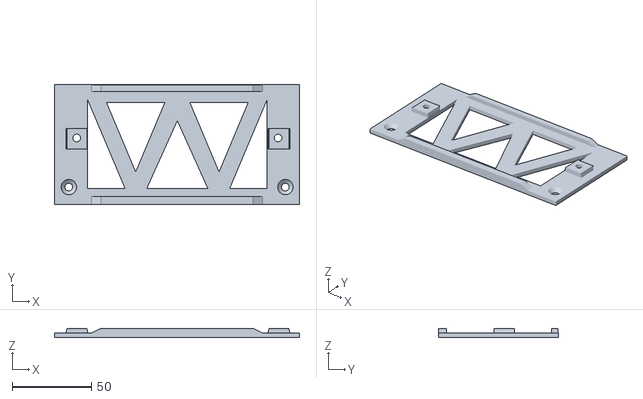
[picture p85: CAD file, 2023-02-26]
gen/mech/ltap_mini_shallow.stl
155.0 x 76.0 x 6.00
