Wakoma/nimble/gen/mech/keystone_patch_panel_2_units_short.stl

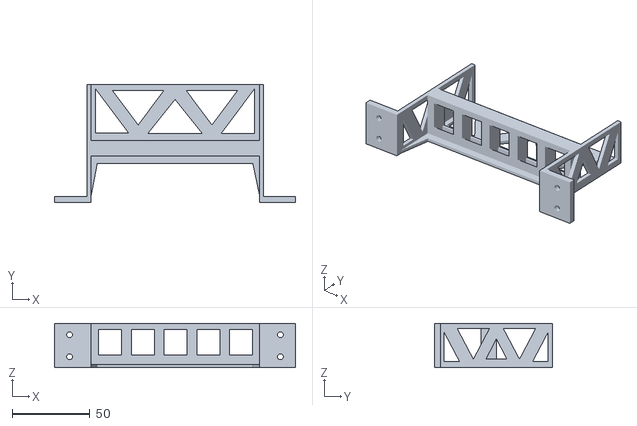
[picture p86: CAD file, 2023-02-26]
gen/mech/keystone_patch_panel_2_units_short.stl
155.0 x 76.0 x 28.4
