Wakoma/nimble/gen/mech/usg_top.stl

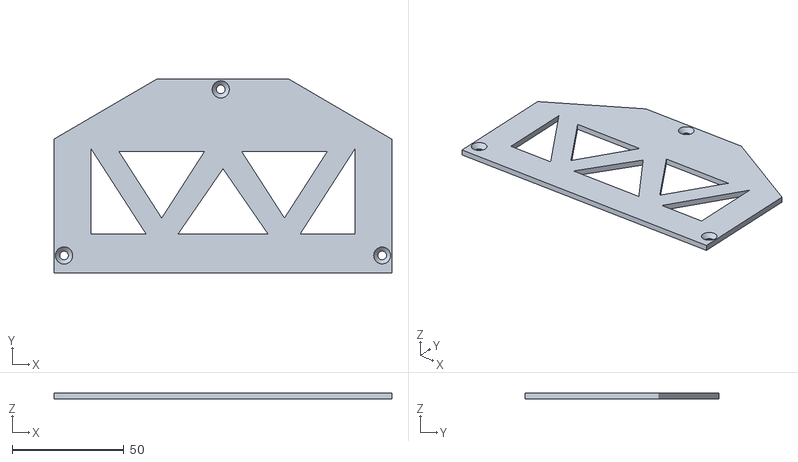
[picture p87: CAD file, 2023-02-26]
gen/mech/usg_top.stl
151.5 x 86.9 x 2.80
