Wakoma/nimble/gen/mech/ap_mount_for_1430_top.stl

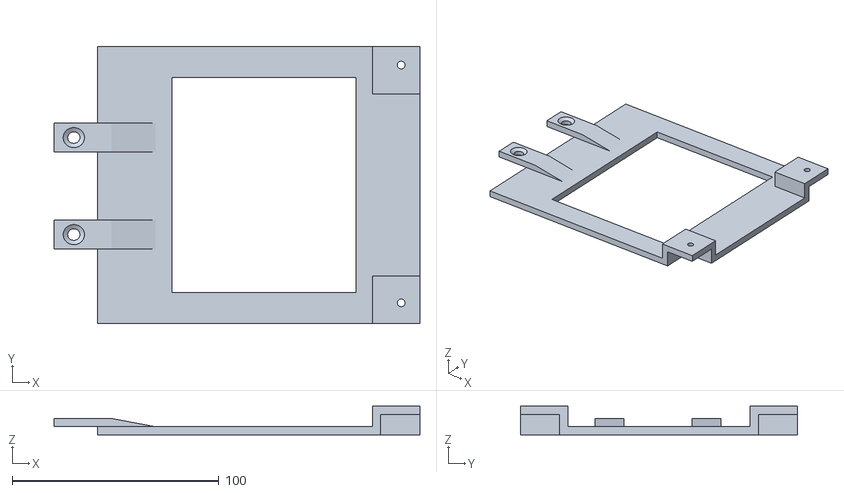
[picture p88: CAD file, 2021-04-23]
gen/mech/ap_mount_for_1430_top.stl
177.0 x 134.0 x 14.0
