Wakoma/nimble/gen/mech/keystone_patch_panel_2_units.stl

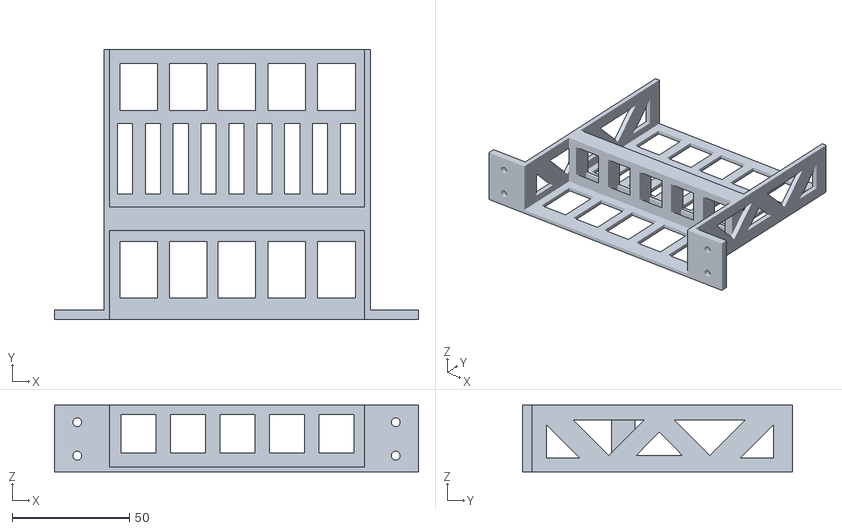
[picture p89: CAD file, 2021-04-23]
gen/mech/keystone_patch_panel_2_units.stl
155.0 x 115.0 x 28.4
