Wakoma/nimble/gen/mech/rack_leg_21_units.stl

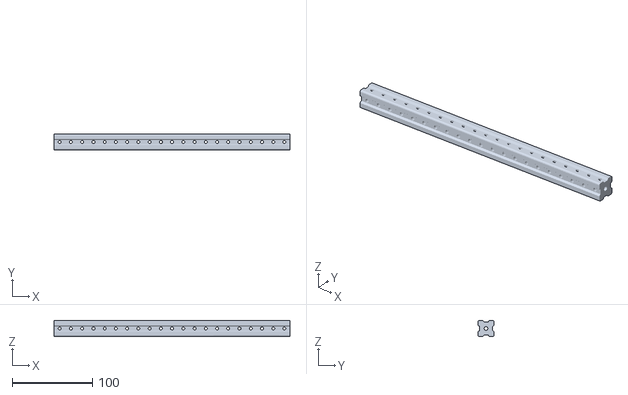
[picture p90: CAD file, 2021-04-23]
gen/mech/rack_leg_21_units.stl
294.0 x 20.0 x 20.0
