Wakoma/nimble/gen/mech/ap_mount_for_1430_bottom.stl

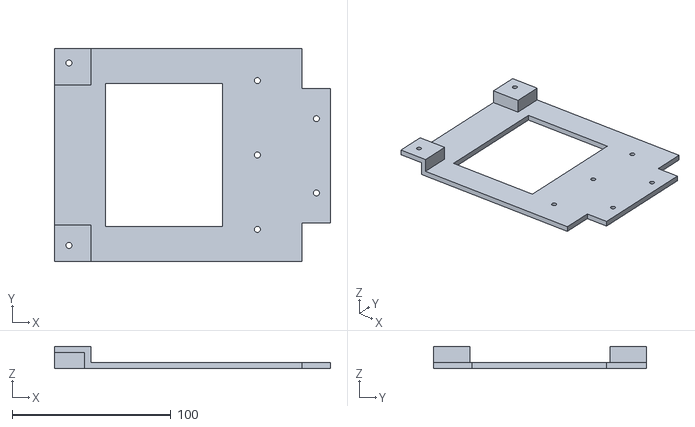
[picture p91: CAD file, 2021-04-23]
gen/mech/ap_mount_for_1430_bottom.stl
174.0 x 134.0 x 14.0
