Wakoma/nimble/gen/mech/sg-1100_shelf.stl

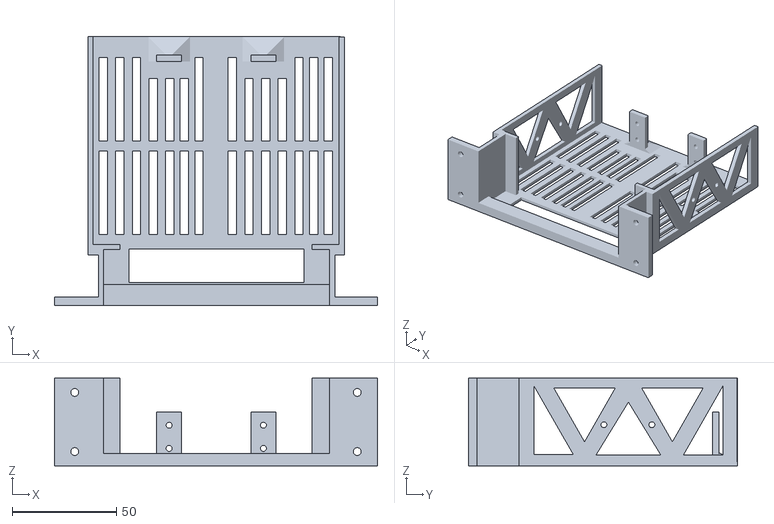
[picture p92: CAD file, 2021-04-23]
gen/mech/sg-1100_shelf.stl
155.0 x 129.0 x 42.2
