Wakoma/nimble/gen/mech/omni_20_top.stl

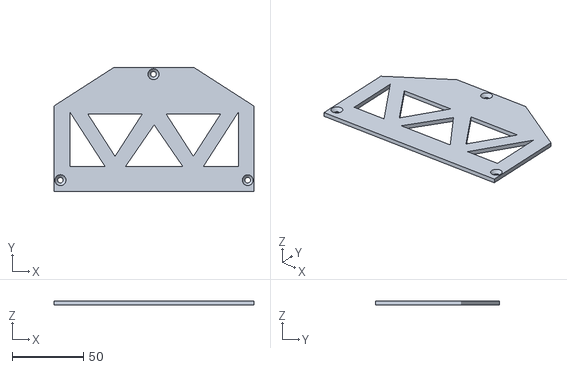
[picture p93: CAD file, 2021-04-23]
gen/mech/omni_20_top.stl
140.5 x 86.9 x 2.80
