Wakoma/nimble/gen/mech/stuff_shelf_thin.stl

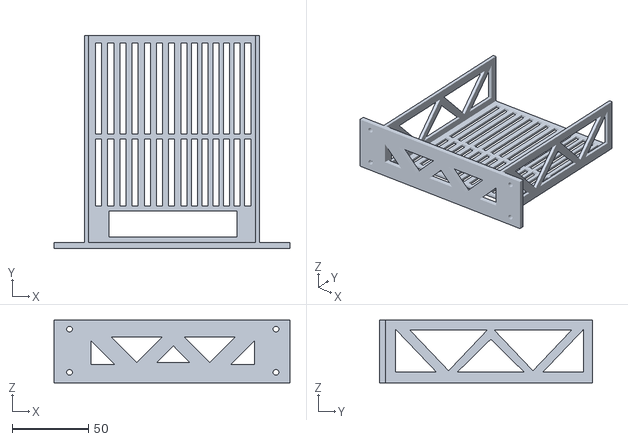
[picture p94: CAD file, 2021-04-23]
gen/mech/stuff_shelf_thin.stl
155.0 x 139.8 x 41.2
