Wakoma/nimble/gen/mech/omni_20.stl

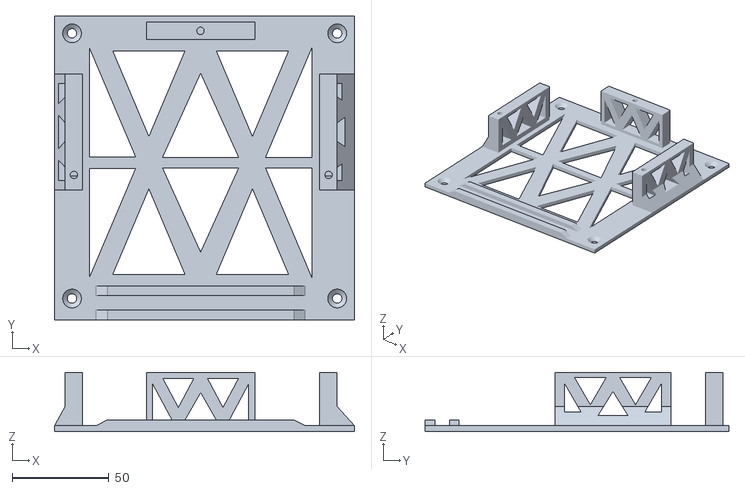
[picture p95: CAD file, 2021-04-23]
gen/mech/omni_20.stl
155.0 x 157.0 x 30.5
