Wakoma/nimble/gen/mech/usw-flex_shelf.stl

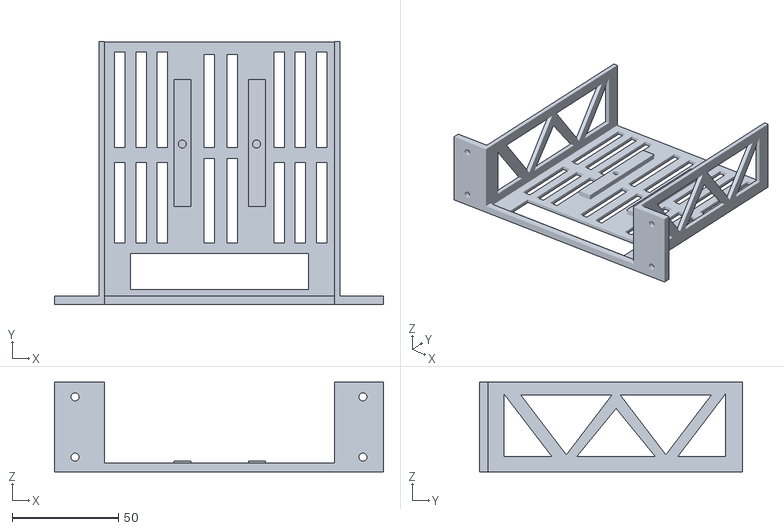
[picture p96: CAD file, 2021-04-23]
gen/mech/usw-flex_shelf.stl
155.0 x 123.8 x 42.2
