Wakoma/nimble/gen/mech/rpi_4b_shelf.stl

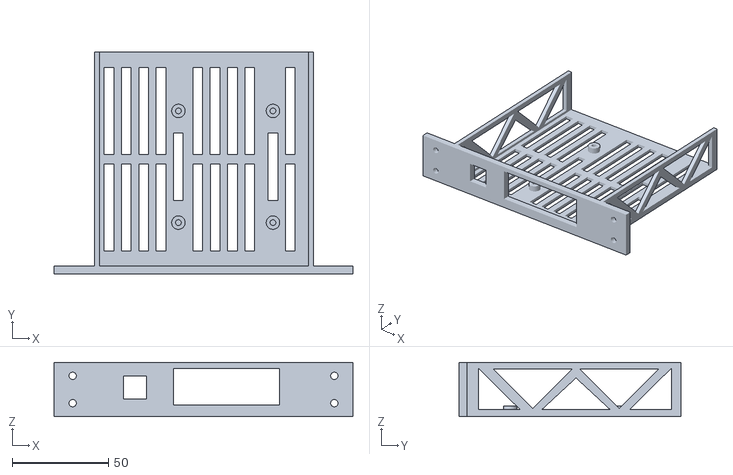
[picture p97: CAD file, 2020-07-05]
gen/mech/rpi_4b_shelf.stl
155.0 x 115.0 x 28.0
