Wakoma/nimble/gen/mech/3.5_hdd_shelf.stl

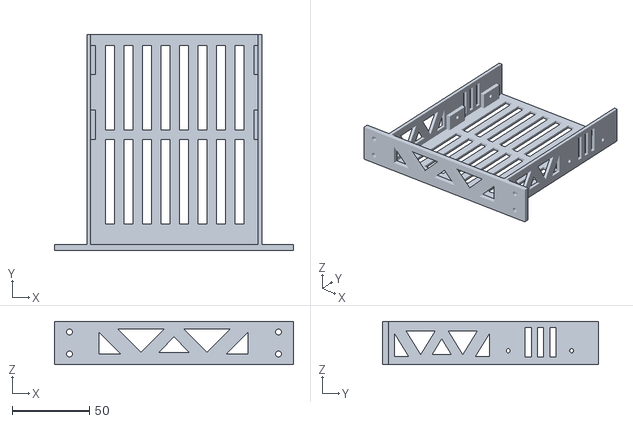
[picture p98: CAD file, 2020-07-03]
gen/mech/3.5_hdd_shelf.stl
155.0 x 140.0 x 28.0
