Wakoma/nimble/gen/mech/mikrotik_shelf.stl

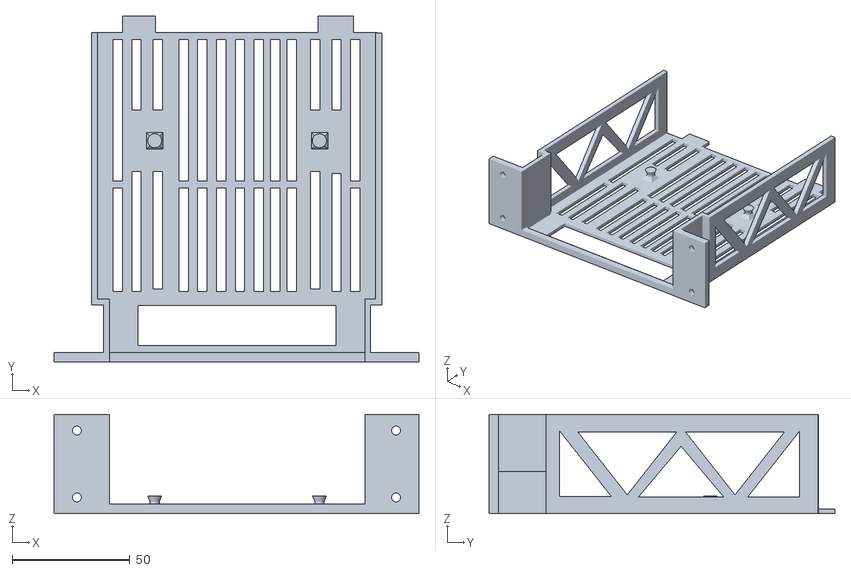
[picture p99: CAD file, 2020-07-03]
gen/mech/mikrotik_shelf.stl
155.0 x 147.0 x 42.2
