Wakoma/nimble/gen/mech/ap_mount_for_1430.stl

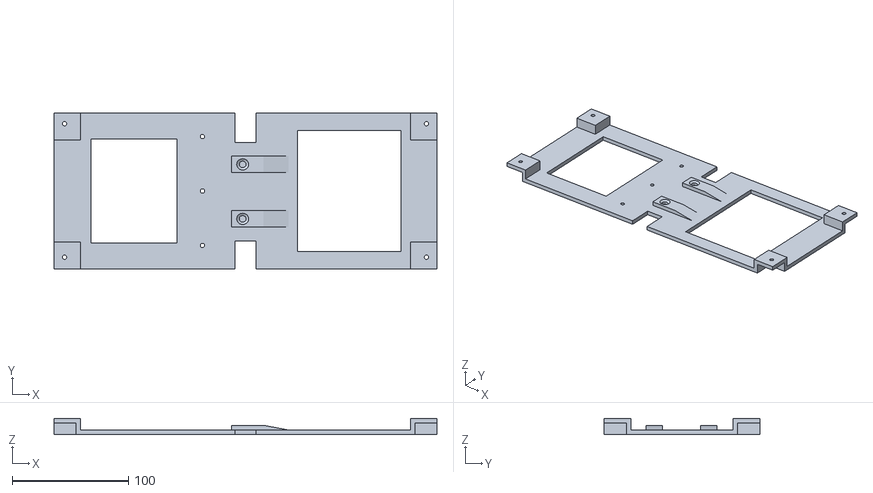
[picture p100: CAD file, 2020-07-03]
gen/mech/ap_mount_for_1430.stl
330.0 x 134.0 x 14.0
