Wakoma/nimble/gen/mech/patch_panel_2_units.stl

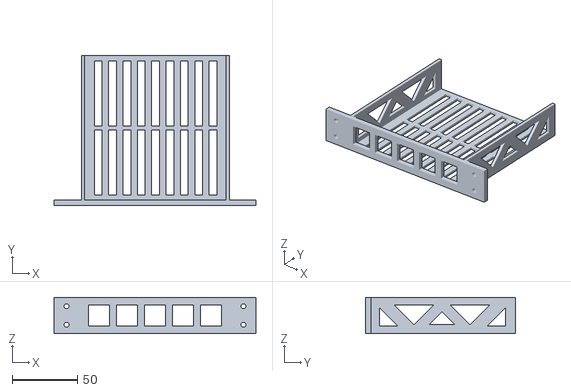
[picture p101: CAD file, 2020-07-03]
gen/mech/patch_panel_2_units.stl
155.0 x 115.0 x 28.0
