Wakoma/nimble/gen/mech/top.stl

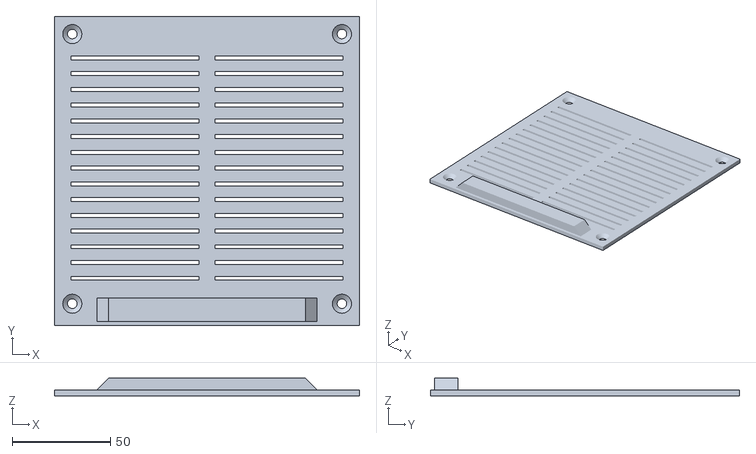
[picture p102: CAD file, 2020-07-03]
gen/mech/top.stl
155.0 x 157.0 x 9.00
