Wakoma/nimble/gen/mech/generic_shelf.stl

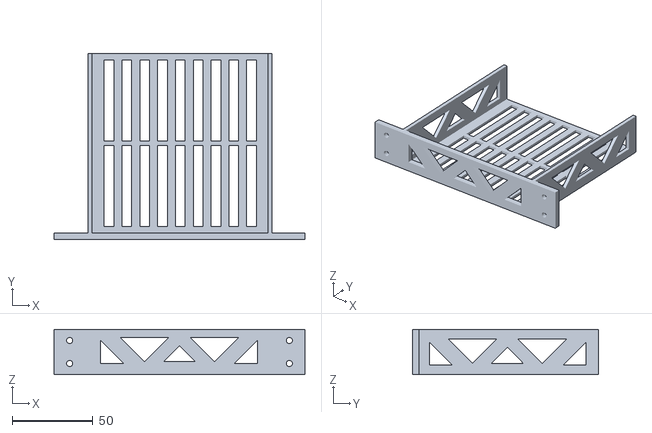
[picture p103: CAD file, 2020-07-03]
gen/mech/generic_shelf.stl
155.0 x 115.0 x 28.0
