Wakoma/nimble/gen/mech/usb_hub_shelf.stl

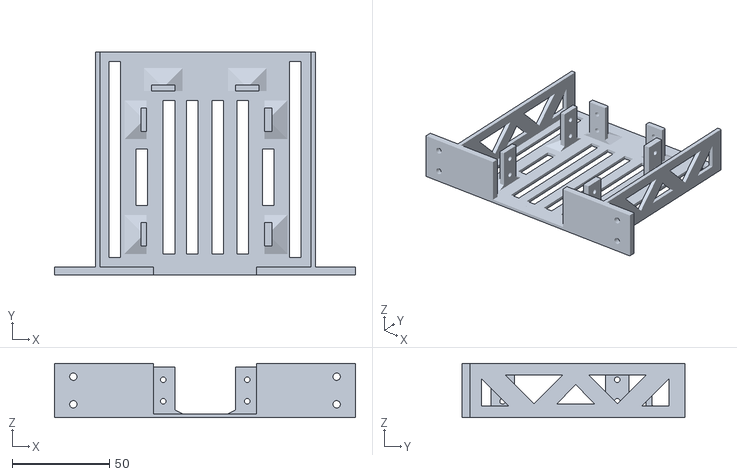
[picture p104: CAD file, 2020-07-03]
gen/mech/usb_hub_shelf.stl
155.0 x 115.0 x 28.0
